Matthewjg95/PlatypusOne/services/ai/README.md

# services/ai

Skeleton — see docs/ROADMAP.md for the milestone that implements this service. Must follow the layering rule: depends only on platform interfaces and other services.
