Matthewjg95/PlatypusOne/docs/media/IMG_8050.JPG

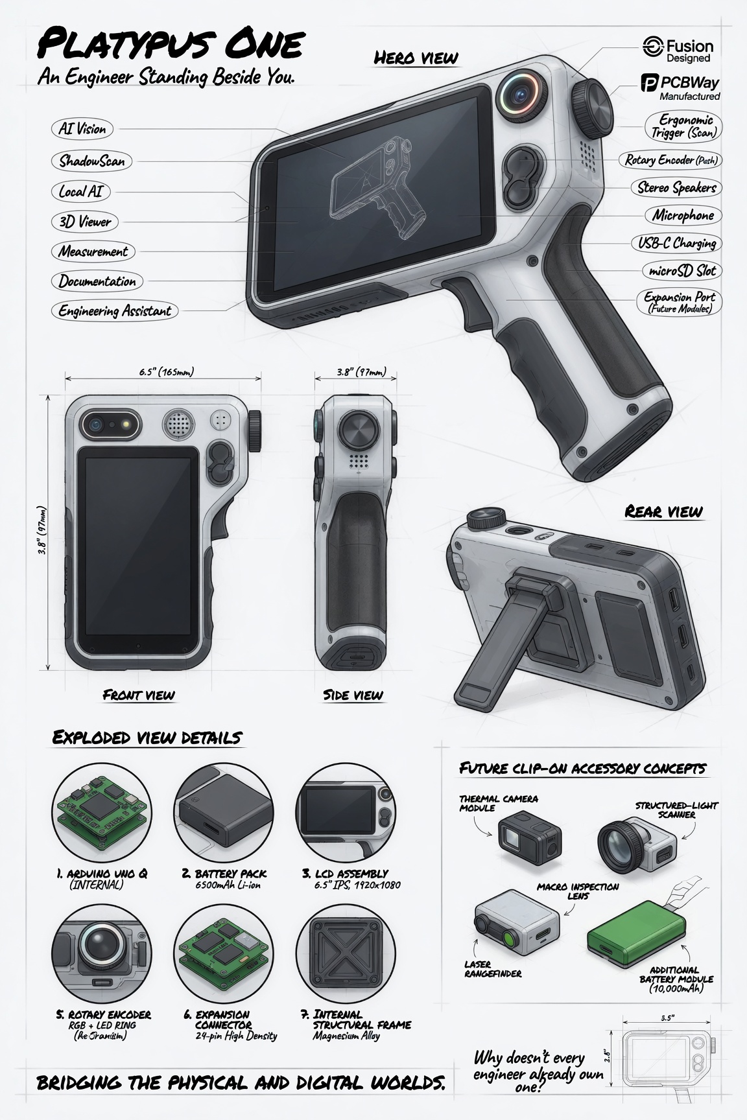
docs/media/IMG_8050.JPG
