Matthewjg95/PlatypusOne/docs/media/IMG_8051.JPG

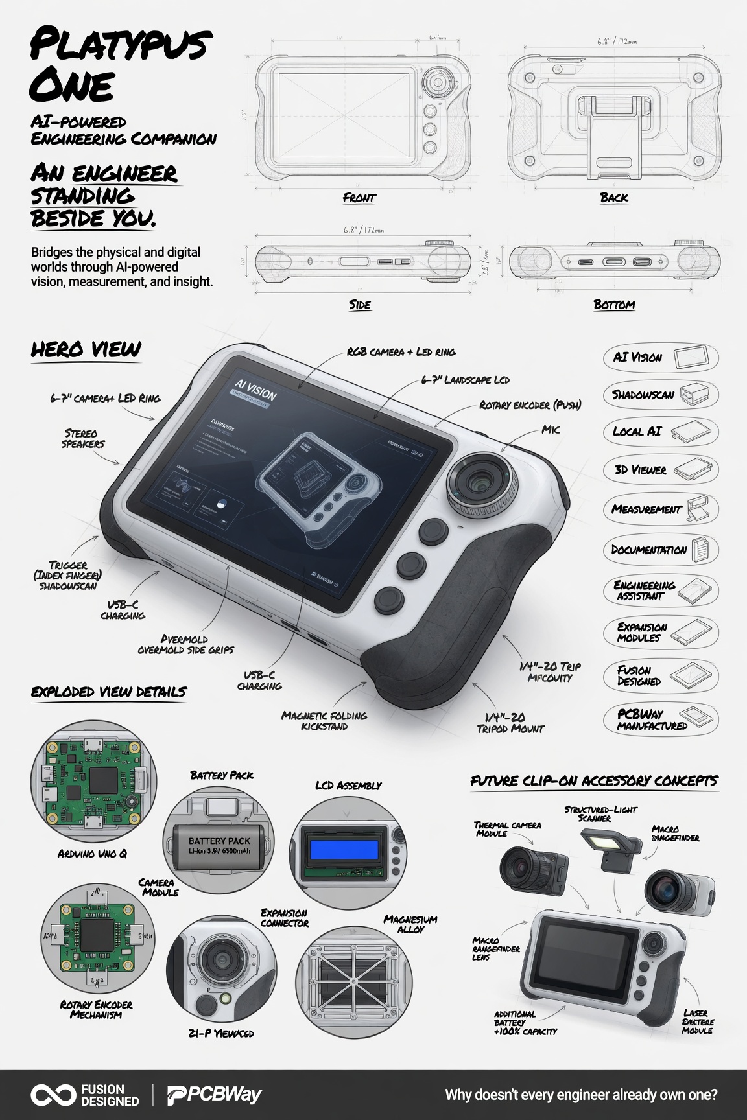
docs/media/IMG_8051.JPG
