Matthewjg95/PlatypusOne/docs/media/IMG_8052.JPG

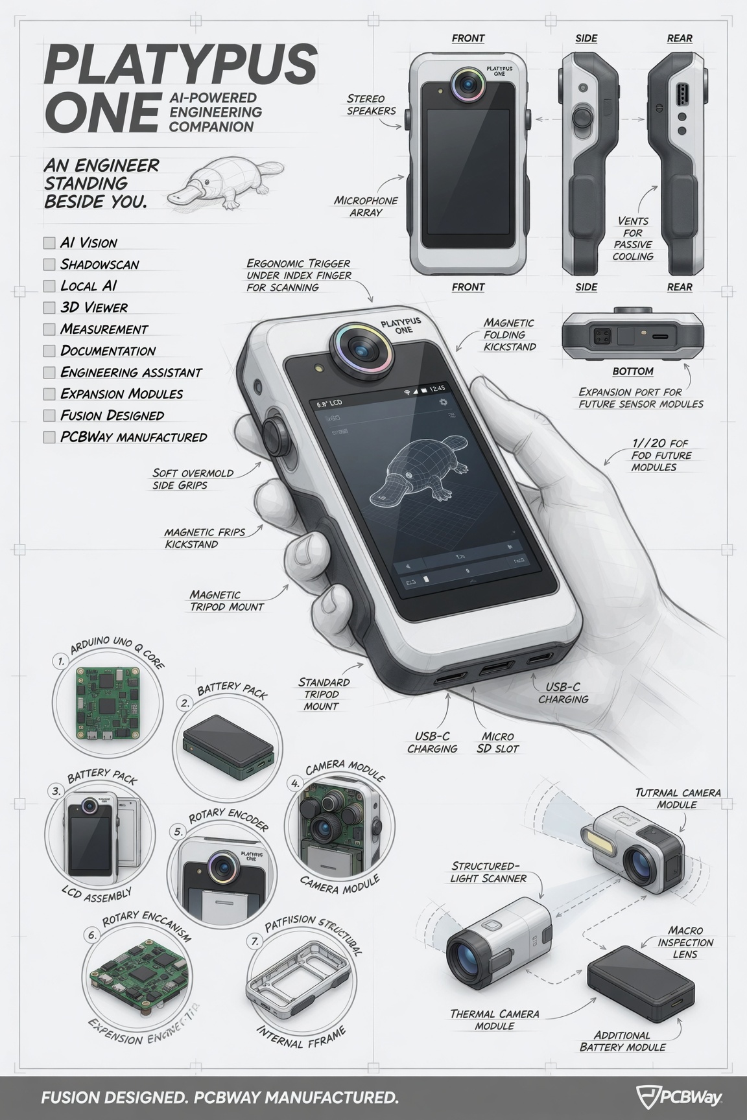
docs/media/IMG_8052.JPG
