Matthewjg95/PlatypusOne/docs/media/renders/scout-card-bolt.png

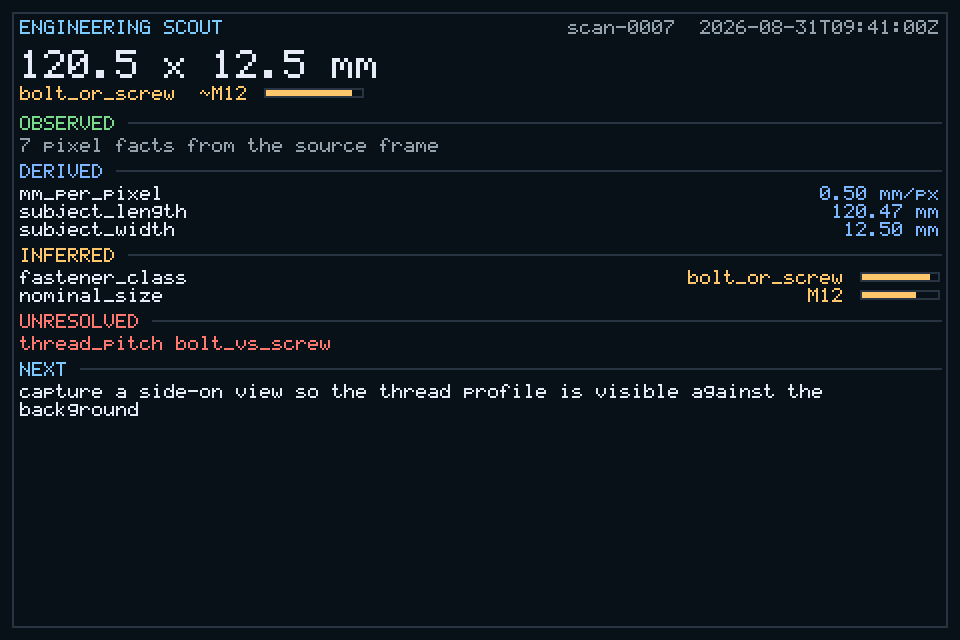
docs/media/renders/scout-card-bolt.png
