Matthewjg95/PlatypusOne/docs/hardware/calibration_sheet.pdf

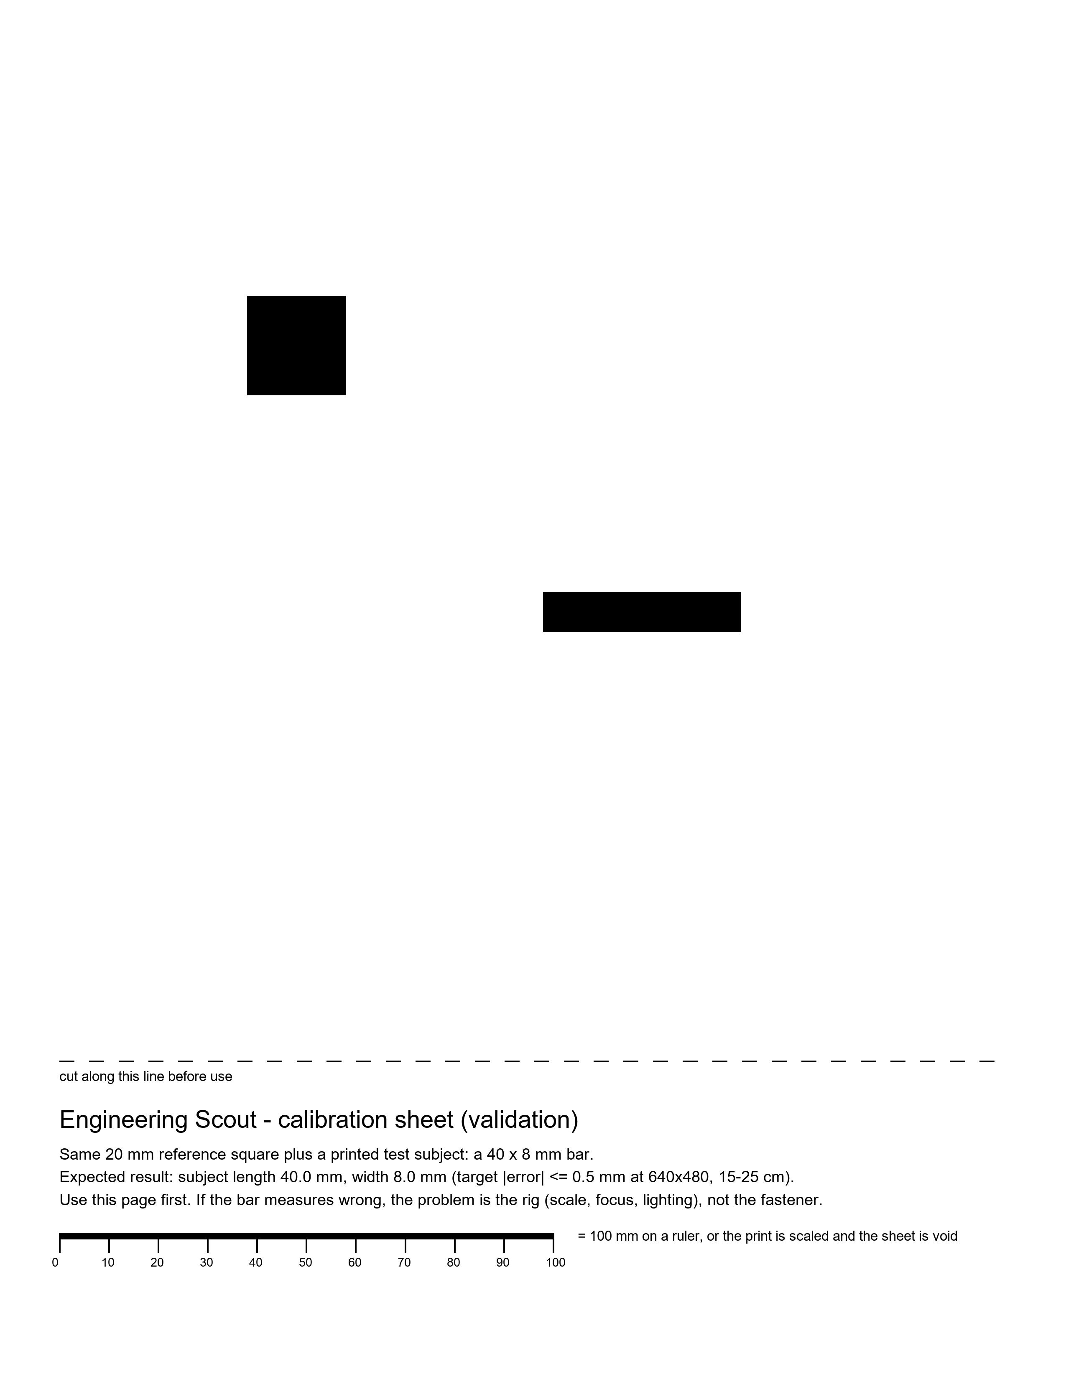
[picture p13: page 1]
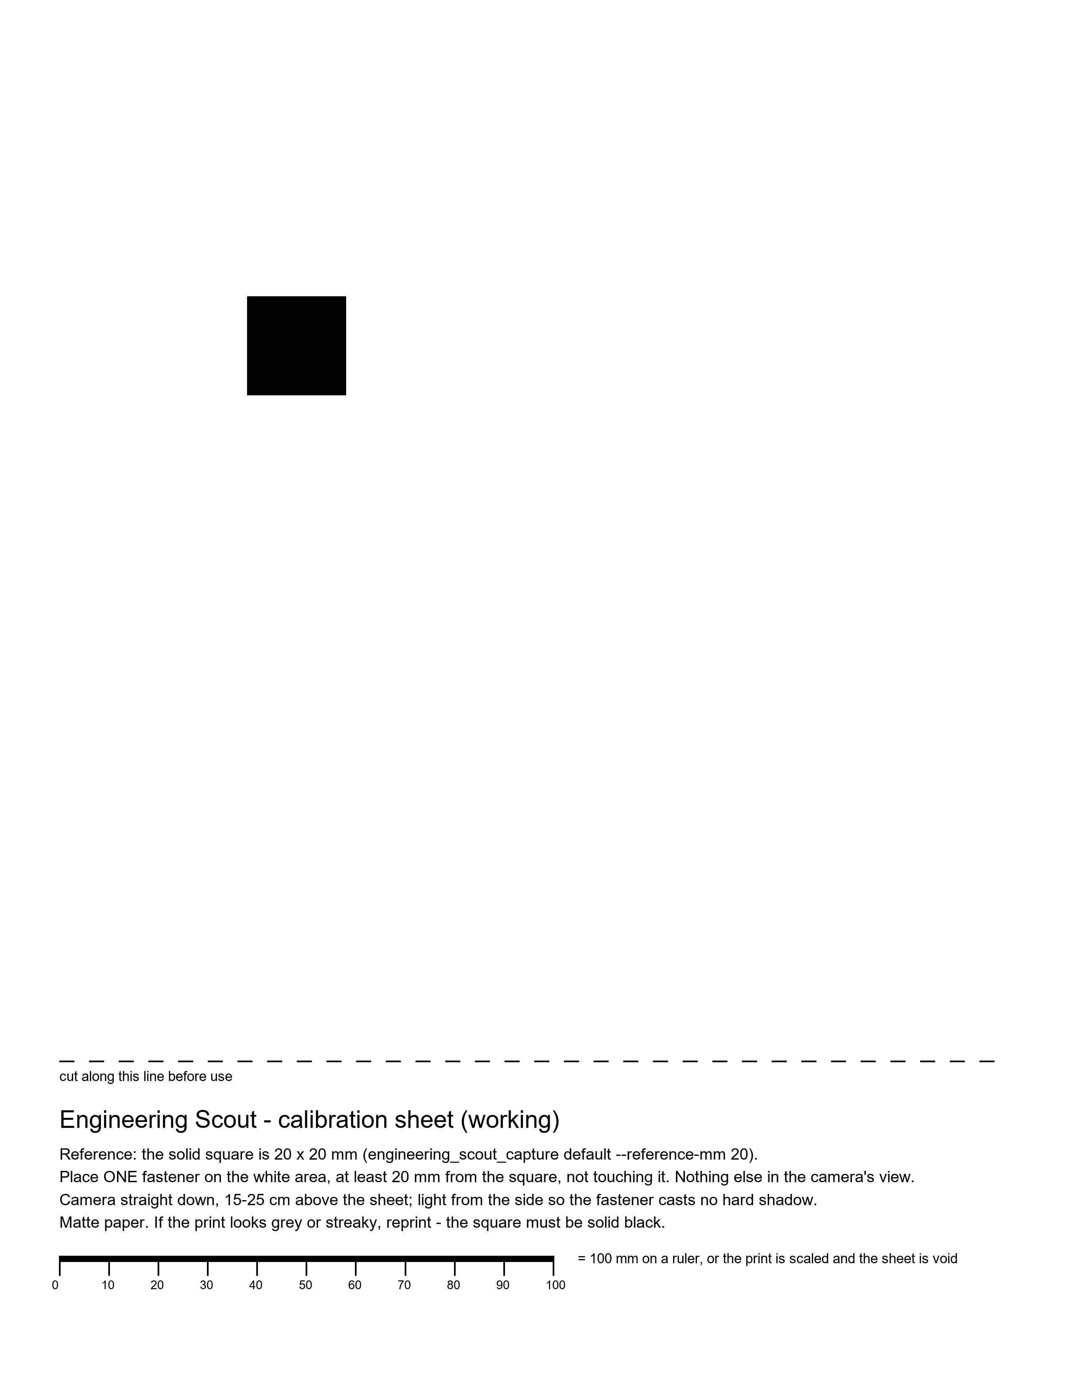
[picture p14: page 2]
