Matthewjg95/PlatypusOne/hardware/pcb/perception_head_rev_a/debug_test.kicad_sch

## KiCad design hardware/pcb/perception_head_rev_a/debug_test.kicad_sch (2026-10-05)

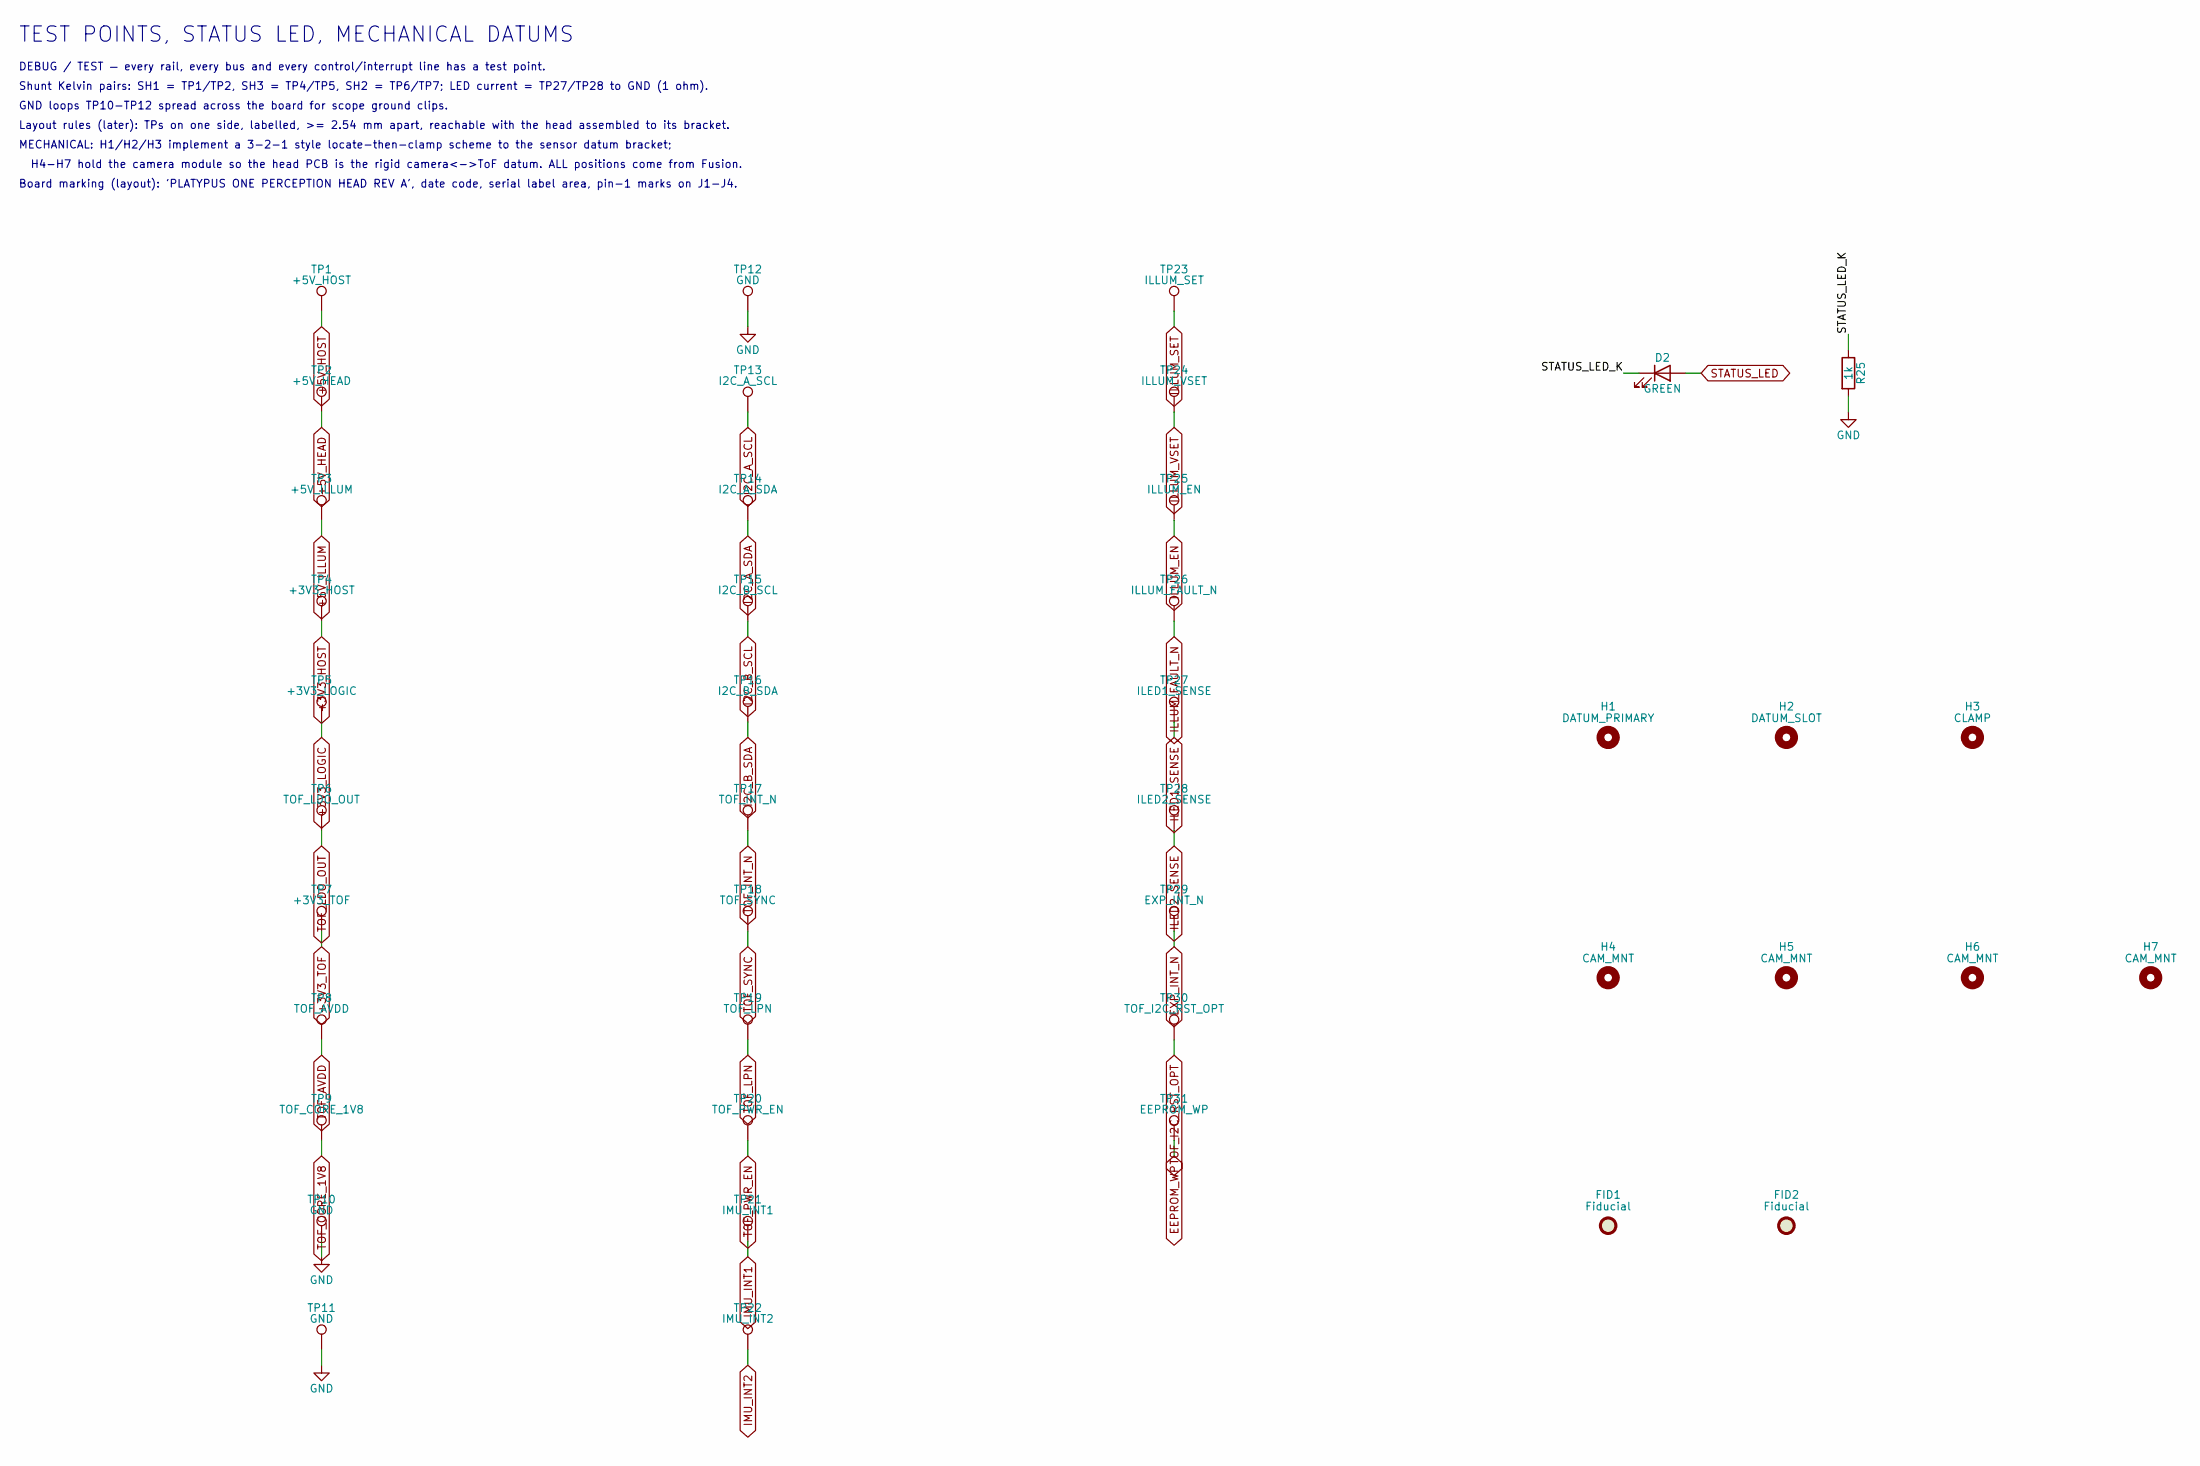
[picture p23: schematic debug_test.kicad_sch]

Parts:
D2: GREEN; LED_0603_1608Metric
FID1, FID2: Fiducial; Fiducial_1mm_Mask2mm
H1: DATUM_PRIMARY; MountingHole_2.2mm_M2
H2: DATUM_SLOT; MountingHole_2.2mm_M2
H3: CLAMP; MountingHole_2.2mm_M2
H4, H5, H6, H7: CAM_MNT; MountingHole_2.2mm_M2
R25: 1k; R_0603_1608Metric
TP1: +5V_HOST; TestPoint_Pad_D1.5mm
TP2: +5V_HEAD; TestPoint_Pad_D1.5mm
TP3: +5V_ILLUM; TestPoint_Pad_D1.5mm
TP4: +3V3_HOST; TestPoint_Pad_D1.5mm
TP5: +3V3_LOGIC; TestPoint_Pad_D1.5mm
TP6: TOF_LDO_OUT; TestPoint_Pad_D1.5mm
TP7: +3V3_TOF; TestPoint_Pad_D1.5mm
TP8: TOF_AVDD; TestPoint_Pad_D1.5mm
TP9: TOF_CORE_1V8; TestPoint_Pad_D1.5mm
TP10, TP11, TP12: GND; TestPoint_Keystone_5019_Miniature
TP13: I2C_A_SCL; TestPoint_Pad_D1.5mm
TP14: I2C_A_SDA; TestPoint_Pad_D1.5mm
TP15: I2C_B_SCL; TestPoint_Pad_D1.5mm
TP16: I2C_B_SDA; TestPoint_Pad_D1.5mm
TP17: TOF_INT_N; TestPoint_Pad_D1.5mm
TP18: TOF_SYNC; TestPoint_Pad_D1.5mm
TP19: TOF_LPN; TestPoint_Pad_D1.5mm
TP20: TOF_PWR_EN; TestPoint_Pad_D1.5mm
TP21: IMU_INT1; TestPoint_Pad_D1.5mm
TP22: IMU_INT2; TestPoint_Pad_D1.5mm
TP23: ILLUM_SET; TestPoint_Pad_D1.5mm
TP24: ILLUM_VSET; TestPoint_Pad_D1.5mm
TP25: ILLUM_EN; TestPoint_Pad_D1.5mm
TP26: ILLUM_FAULT_N; TestPoint_Pad_D1.5mm
TP27: ILED1_SENSE; TestPoint_Pad_D1.5mm
TP28: ILED2_SENSE; TestPoint_Pad_D1.5mm
TP29: EXP_INT_N; TestPoint_Pad_D1.5mm
TP30: TOF_I2C_RST_OPT; TestPoint_Pad_D1.5mm
TP31: EEPROM_WP; TestPoint_Pad_D1.5mm

Connections:
+3V3_HOST: TP4.1
+3V3_LOGIC: TP5.1
+3V3_TOF: TP7.1
+5V_HEAD: TP2.1
+5V_HOST: TP1.1
+5V_ILLUM: TP3.1
EEPROM_WP: TP31.1
EXP_INT_N: TP29.1
GND: R25.2, TP10.1, TP11.1, TP12.1
I2C_A_SCL: TP13.1
I2C_A_SDA: TP14.1
I2C_B_SCL: TP15.1
I2C_B_SDA: TP16.1
ILED1_SENSE: TP27.1
ILED2_SENSE: TP28.1
ILLUM_EN: TP25.1
ILLUM_FAULT_N: TP26.1
ILLUM_SET: TP23.1
ILLUM_VSET: TP24.1
IMU_INT1: TP21.1
IMU_INT2: TP22.1
STATUS_LED: D2.2 (A)
STATUS_LED_K: D2.1 (K), R25.1
TOF_AVDD: TP8.1
TOF_CORE_1V8: TP9.1
TOF_I2C_RST_OPT: TP30.1
TOF_INT_N: TP17.1
TOF_LDO_OUT: TP6.1
TOF_LPN: TP19.1
TOF_PWR_EN: TP20.1
TOF_SYNC: TP18.1

Notes on the sheet:
TEST POINTS, STATUS LED, MECHANICAL DATUMS
DEBUG / TEST — every rail, every bus and every control/interrupt line has a test point.
Shunt Kelvin pairs: SH1 = TP1/TP2, SH3 = TP4/TP5, SH2 = TP6/TP7; LED current = TP27/TP28 to GND (1 ohm).
GND loops TP10-TP12 spread across the board for scope ground clips.
Layout rules (later): TPs on one side, labelled, >= 2.54 mm apart, reachable with the head assembled to its bracket.
MECHANICAL: H1/H2/H3 implement a 3-2-1 style locate-then-clamp scheme to the sensor datum bracket;
H4-H7 hold the camera module so the head PCB is the rigid camera<->ToF datum. ALL positions come from Fusion.
Board marking (layout): 'PLATYPUS ONE PERCEPTION HEAD REV A', date code, serial label area, pin-1 marks on J1-J4.
