Matthewjg95/PlatypusOne/hardware/pcb/perception_head_rev_a/host_interface.kicad_sch

## KiCad design hardware/pcb/perception_head_rev_a/host_interface.kicad_sch (2026-10-05)

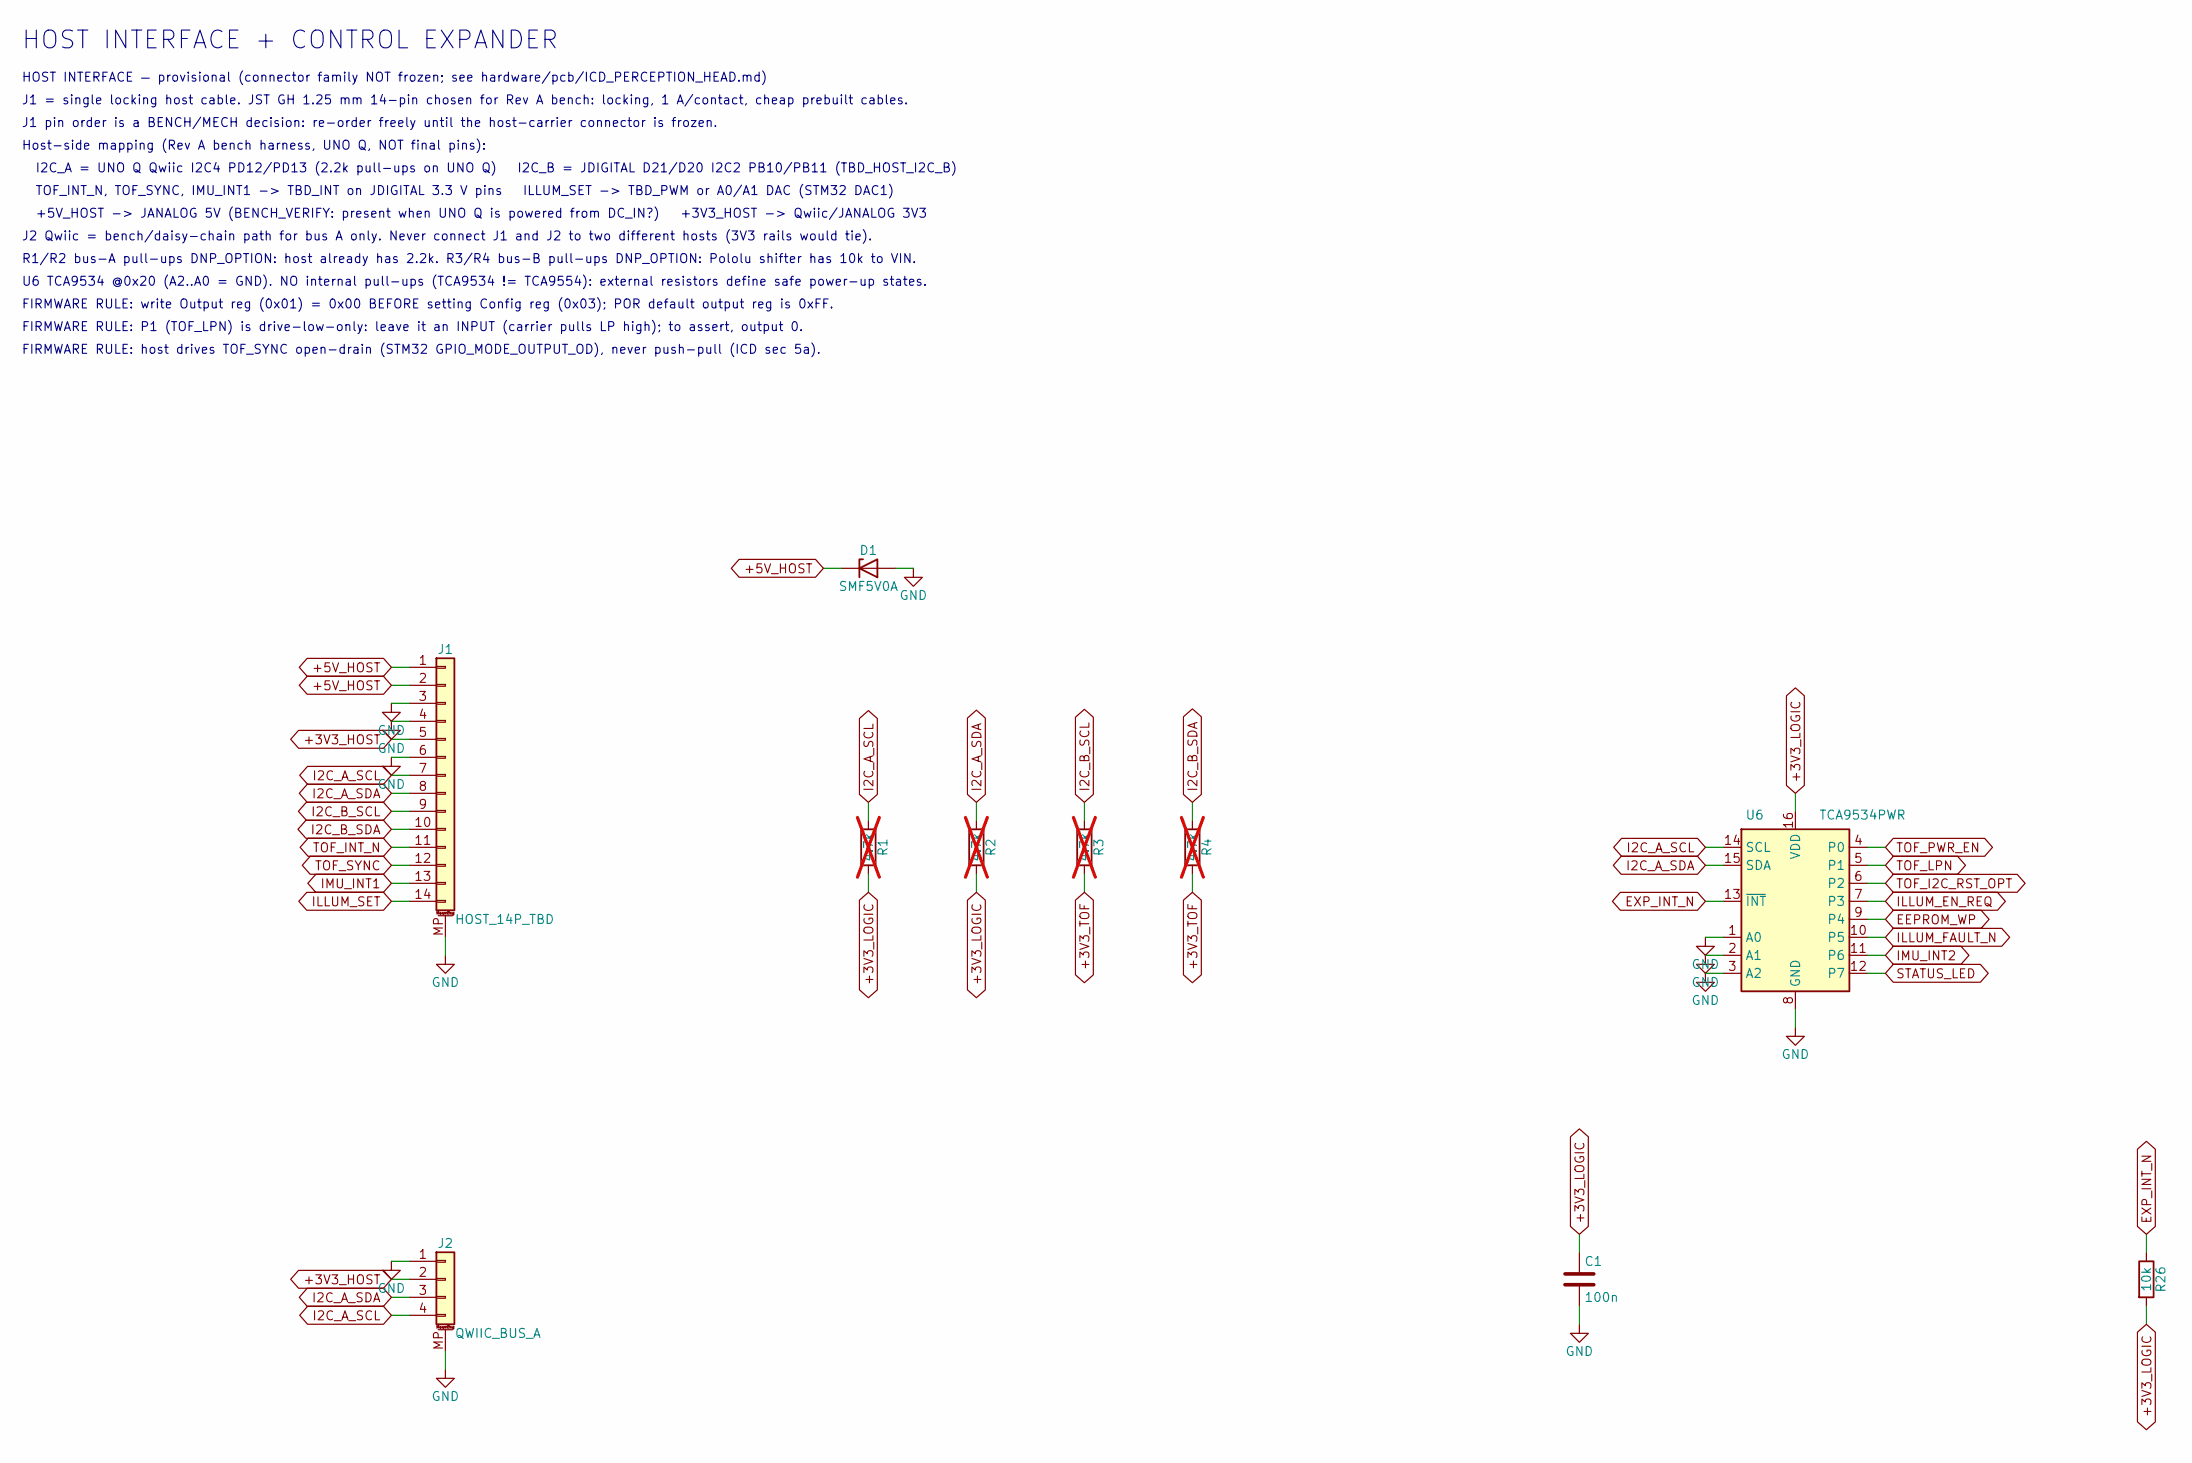
[picture p24: schematic host_interface.kicad_sch]

Parts:
C1: 100n; C_0603_1608Metric
D1: SMF5V0A; D_SMF; MPN SMF5V0A-E3-08
J1: HOST_14P_TBD; JST_GH_SM14B-GHS-TB_1x14-1MP_P1.25mm_Horizontal; MPN SM14B-GHS-TB(LF)(SN)
J2: QWIIC_BUS_A; JST_SH_SM04B-SRSS-TB_1x04-1MP_P1.00mm_Horizontal; MPN SM04B-SRSS-TB(LF)(SN)
R1, R2, R3, R4: 4.7k; R_0603_1608Metric; not fitted
R26: 10k; R_0603_1608Metric
U6: TCA9534PWR; TSSOP-16_4.4x5mm_P0.65mm; MPN TCA9534PWR

Connections:
+3V3_HOST: J1.5, J2.2
+3V3_LOGIC: C1.1, R1.2, R2.2, R26.2, U6.16 (VDD)
+3V3_TOF: R3.2, R4.2
+5V_HOST: D1.1 (K), J1.1, J1.2
EEPROM_WP: U6.9 (P4)
EXP_INT_N: R26.1, U6.13 (~INT)
GND: C1.2, D1.2 (A), J1.3, J1.4, J1.6, J1.MP (MountPin), J2.1, J2.MP (MountPin), U6.1 (A0), U6.2 (A1), U6.3 (A2), U6.8 (GND)
I2C_A_SCL: J1.7, J2.4, R1.1, U6.14 (SCL)
I2C_A_SDA: J1.8, J2.3, R2.1, U6.15 (SDA)
I2C_B_SCL: J1.9, R3.1
I2C_B_SDA: J1.10, R4.1
ILLUM_EN_REQ: U6.7 (P3)
ILLUM_FAULT_N: U6.10 (P5)
ILLUM_SET: J1.14
IMU_INT1: J1.13
IMU_INT2: U6.11 (P6)
STATUS_LED: U6.12 (P7)
TOF_I2C_RST_OPT: U6.6 (P2)
TOF_INT_N: J1.11
TOF_LPN: U6.5 (P1)
TOF_PWR_EN: U6.4 (P0)
TOF_SYNC: J1.12

Notes on the sheet:
HOST INTERFACE + CONTROL EXPANDER
HOST INTERFACE — provisional (connector family NOT frozen; see hardware/pcb/ICD_PERCEPTION_HEAD.md)
J1 = single locking host cable. JST GH 1.25 mm 14-pin chosen for Rev A bench: locking, 1 A/contact, cheap prebuilt cables.
J1 pin order is a BENCH/MECH decision: re-order freely until the host-carrier connector is frozen.
Host-side mapping (Rev A bench harness, UNO Q, NOT final pins):
I2C_A = UNO Q Qwiic I2C4 PD12/PD13 (2.2k pull-ups on UNO Q) I2C_B = JDIGITAL D21/D20 I2C2 PB10/PB11 (TBD_HOST_I2C_B)
TOF_INT_N, TOF_SYNC, IMU_INT1 -> TBD_INT on JDIGITAL 3.3 V pins ILLUM_SET -> TBD_PWM or A0/A1 DAC (STM32 DAC1)
+5V_HOST -> JANALOG 5V (BENCH_VERIFY: present when UNO Q is powered from DC_IN?) +3V3_HOST -> Qwiic/JANALOG 3V3
J2 Qwiic = bench/daisy-chain path for bus A only. Never connect J1 and J2 to two different hosts (3V3 rails would tie).
R1/R2 bus-A pull-ups DNP_OPTION: host already has 2.2k. R3/R4 bus-B pull-ups DNP_OPTION: Pololu shifter has 10k to VIN.
U6 TCA9534 @0x20 (A2..A0 = GND). NO internal pull-ups (TCA9534 != TCA9554): external resistors define safe power-up states.
FIRMWARE RULE: write Output reg (0x01) = 0x00 BEFORE setting Config reg (0x03); POR default output reg is 0xFF.
FIRMWARE RULE: P1 (TOF_LPN) is drive-low-only: leave it an INPUT (carrier pulls LP high); to assert, output 0.
FIRMWARE RULE: host drives TOF_SYNC open-drain (STM32 GPIO_MODE_OUTPUT_OD), never push-pull (ICD sec 5a).
