Matthewjg95/PlatypusOne/hardware/pcb/perception_head_rev_a/id_calibration.kicad_sch

## KiCad design hardware/pcb/perception_head_rev_a/id_calibration.kicad_sch (2026-10-05)

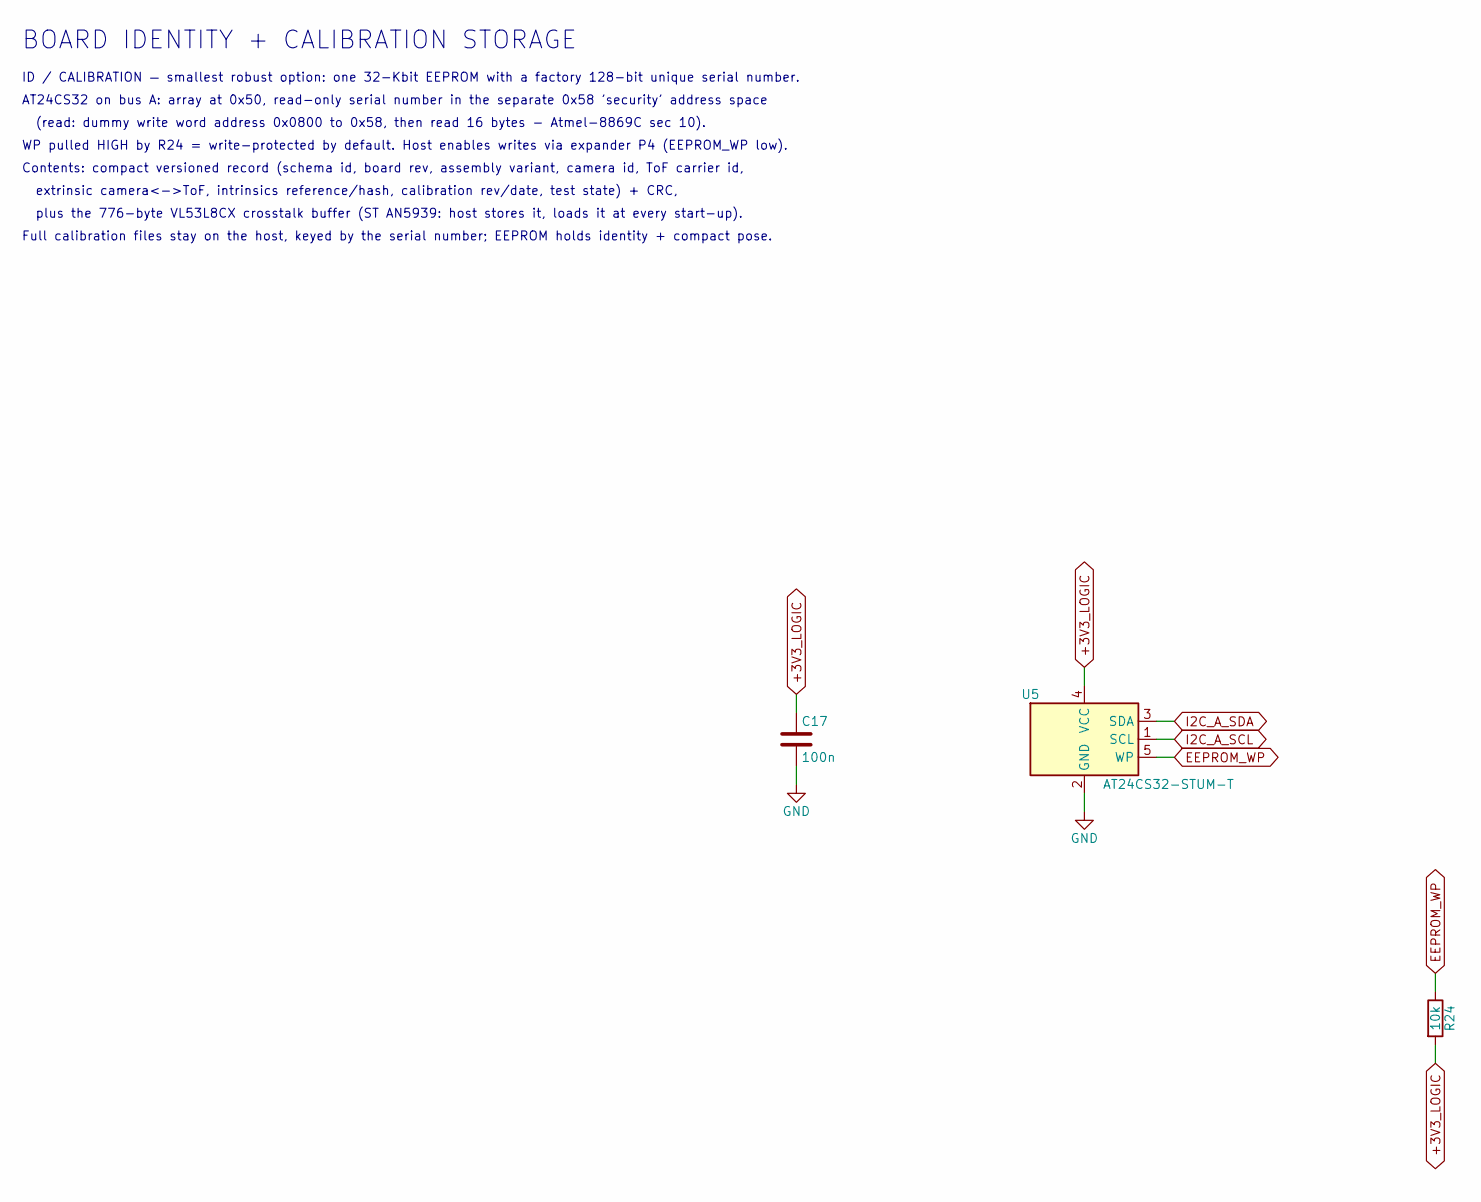
[picture p25: schematic id_calibration.kicad_sch]

Parts:
C17: 100n; C_0603_1608Metric
R24: 10k; R_0603_1608Metric
U5: AT24CS32-STUM-T; SOT-23-5; MPN AT24CS32-STUM-T

Connections:
+3V3_LOGIC: C17.1, R24.2, U5.4 (VCC)
EEPROM_WP: R24.1, U5.5 (WP)
GND: C17.2, U5.2 (GND)
I2C_A_SCL: U5.1 (SCL)
I2C_A_SDA: U5.3 (SDA)

Notes on the sheet:
BOARD IDENTITY + CALIBRATION STORAGE
ID / CALIBRATION — smallest robust option: one 32-Kbit EEPROM with a factory 128-bit unique serial number.
AT24CS32 on bus A: array at 0x50, read-only serial number in the separate 0x58 'security' address space
(read: dummy write word address 0x0800 to 0x58, then read 16 bytes - Atmel-8869C sec 10).
WP pulled HIGH by R24 = write-protected by default. Host enables writes via expander P4 (EEPROM_WP low).
Contents: compact versioned record (schema id, board rev, assembly variant, camera id, ToF carrier id,
extrinsic camera<->ToF, intrinsics reference/hash, calibration rev/date, test state) + CRC,
plus the 776-byte VL53L8CX crosstalk buffer (ST AN5939: host stores it, loads it at every start-up).
Full calibration files stay on the host, keyed by the serial number; EEPROM holds identity + compact pose.
