Matthewjg95/PlatypusOne/hardware/pcb/perception_head_rev_a/illumination.kicad_sch

## KiCad design hardware/pcb/perception_head_rev_a/illumination.kicad_sch (2026-10-05)

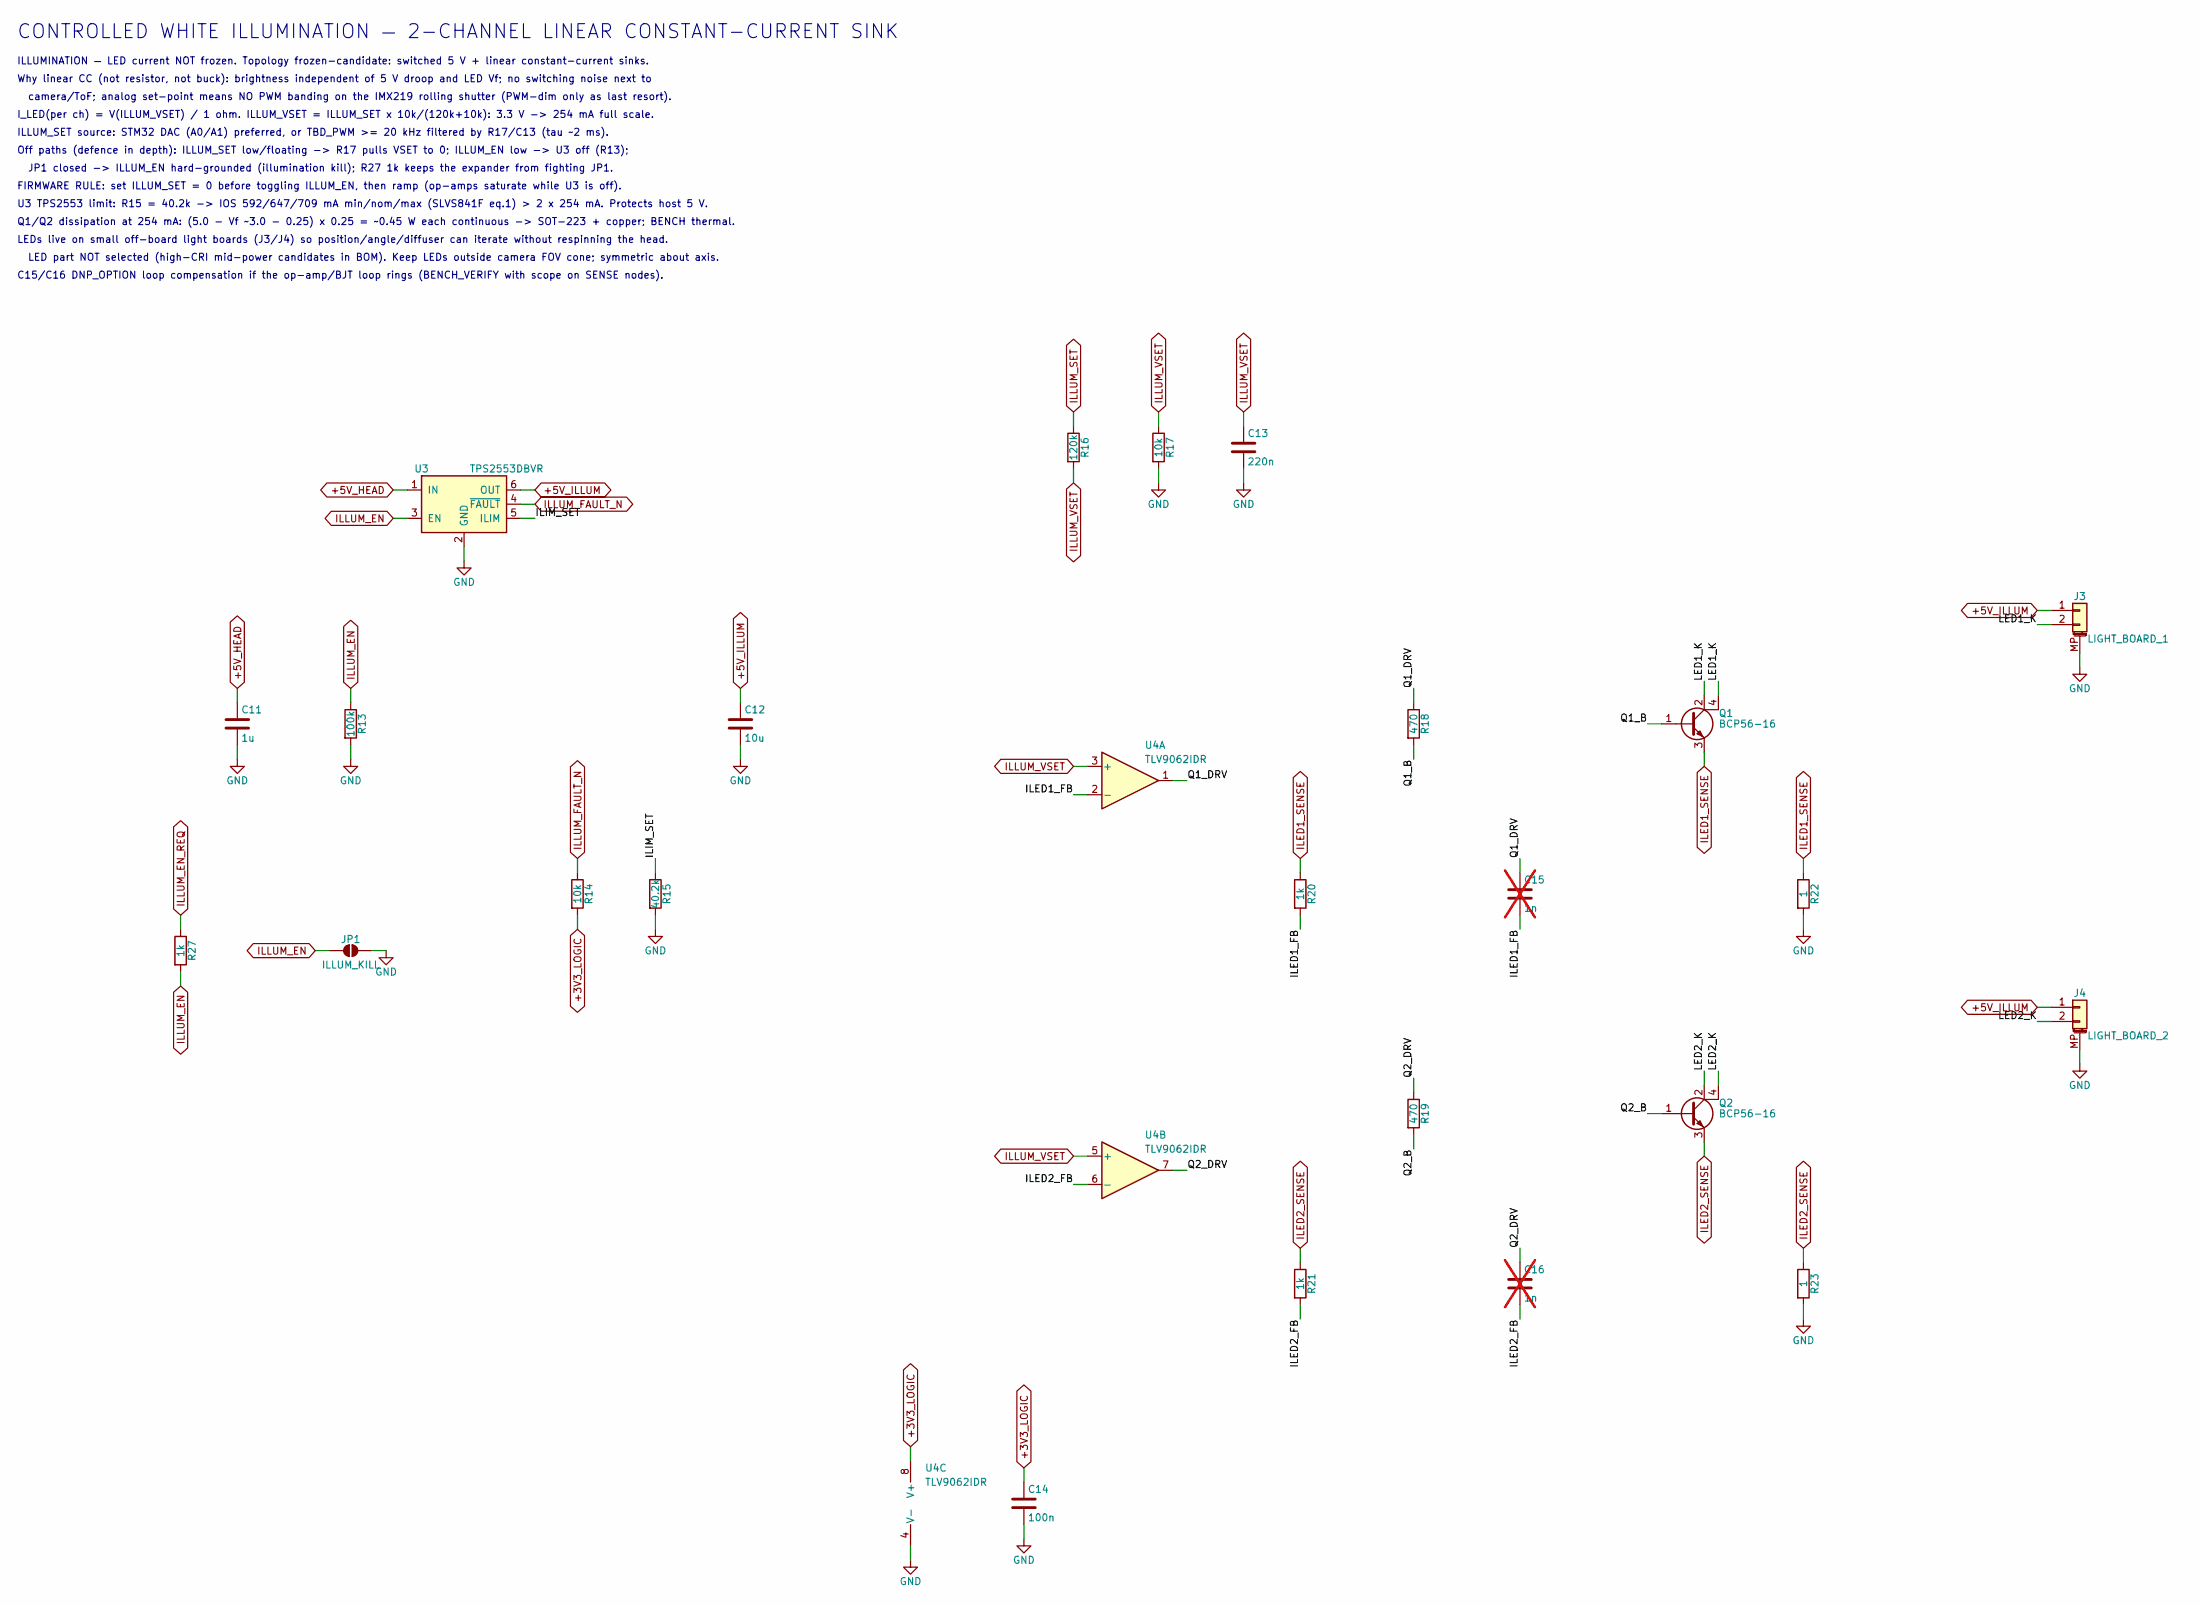
[picture p26: schematic illumination.kicad_sch]

Parts:
C11: 1u; C_0603_1608Metric
C12: 10u; C_0805_2012Metric
C13: 220n; C_0603_1608Metric
C14: 100n; C_0603_1608Metric
C15, C16: 1n; C_0603_1608Metric; not fitted
J3: LIGHT_BOARD_1; JST_GH_SM02B-GHS-TB_1x02-1MP_P1.25mm_Horizontal; MPN SM02B-GHS-TB(LF)(SN)
J4: LIGHT_BOARD_2; JST_GH_SM02B-GHS-TB_1x02-1MP_P1.25mm_Horizontal; MPN SM02B-GHS-TB(LF)(SN)
JP1: ILLUM_KILL; SolderJumper-2_P1.3mm_Open_RoundedPad1.0x1.5mm
Q1, Q2: BCP56-16; SOT-223-3_TabPin2; MPN BCP56-16,115
R13: 100k; R_0603_1608Metric
R14, R17: 10k; R_0603_1608Metric
R15: 40.2k; R_0603_1608Metric
R16: 120k; R_0603_1608Metric
R18, R19: 470; R_0603_1608Metric
R20, R21, R27: 1k; R_0603_1608Metric
R22, R23: 1; R_1206_3216Metric
U3: TPS2553DBVR; SOT-23-6; MPN TPS2553DBVR
U4: TLV9062IDR; SOIC-8_3.9x4.9mm_P1.27mm; MPN TLV9062IDR

Connections:
+3V3_LOGIC: C14.1, R14.2, U4.8 (V+)
+5V_HEAD: C11.1, U3.1 (IN)
+5V_ILLUM: C12.1, J3.1, J4.1, U3.6 (OUT)
GND: C11.2, C12.2, C13.2, C14.2, J3.MP (MountPin), J4.MP (MountPin), JP1.2 (B), R13.2, R15.2, R17.2, R22.2, R23.2, U3.2 (GND), U4.4 (V-)
ILED1_FB: C15.2, R20.2, U4.2 (-)
ILED1_SENSE: Q1.3 (E), R20.1, R22.1
ILED2_FB: C16.2, R21.2, U4.6 (-)
ILED2_SENSE: Q2.3 (E), R21.1, R23.1
ILIM_SET: R15.1, U3.5 (ILIM)
ILLUM_EN: JP1.1 (A), R13.1, R27.2, U3.3 (EN)
ILLUM_EN_REQ: R27.1
ILLUM_FAULT_N: R14.1, U3.4 (~FAULT)
ILLUM_SET: R16.1
ILLUM_VSET: C13.1, R16.2, R17.1, U4.3 (+), U4.5 (+)
LED1_K: J3.2, Q1.2 (C), Q1.4 (C)
LED2_K: J4.2, Q2.2 (C), Q2.4 (C)
Q1_B: Q1.1 (B), R18.2
Q1_DRV: C15.1, R18.1, U4.1
Q2_B: Q2.1 (B), R19.2
Q2_DRV: C16.1, R19.1, U4.7

Notes on the sheet:
CONTROLLED WHITE ILLUMINATION — 2-CHANNEL LINEAR CONSTANT-CURRENT SINK
ILLUMINATION — LED current NOT frozen. Topology frozen-candidate: switched 5 V + linear constant-current sinks.
Why linear CC (not resistor, not buck): brightness independent of 5 V droop and LED Vf; no switching noise next to
camera/ToF; analog set-point means NO PWM banding on the IMX219 rolling shutter (PWM-dim only as last resort).
I_LED(per ch) = V(ILLUM_VSET) / 1 ohm. ILLUM_VSET = ILLUM_SET x 10k/(120k+10k): 3.3 V -> 254 mA full scale.
ILLUM_SET source: STM32 DAC (A0/A1) preferred, or TBD_PWM >= 20 kHz filtered by R17/C13 (tau ~2 ms).
Off paths (defence in depth): ILLUM_SET low/floating -> R17 pulls VSET to 0; ILLUM_EN low -> U3 off (R13);
JP1 closed -> ILLUM_EN hard-grounded (illumination kill); R27 1k keeps the expander from fighting JP1.
FIRMWARE RULE: set ILLUM_SET = 0 before toggling ILLUM_EN, then ramp (op-amps saturate while U3 is off).
U3 TPS2553 limit: R15 = 40.2k -> IOS 592/647/709 mA min/nom/max (SLVS841F eq.1) > 2 x 254 mA. Protects host 5 V.
Q1/Q2 dissipation at 254 mA: (5.0 - Vf ~3.0 - 0.25) x 0.25 = ~0.45 W each continuous -> SOT-223 + copper; BENCH thermal.
LEDs live on small off-board light boards (J3/J4) so position/angle/diffuser can iterate without respinning the head.
LED part NOT selected (high-CRI mid-power candidates in BOM). Keep LEDs outside camera FOV cone; symmetric about axis.
C15/C16 DNP_OPTION loop compensation if the op-amp/BJT loop rings (BENCH_VERIFY with scope on SENSE nodes).
