Matthewjg95/PlatypusOne/hardware/pcb/perception_head_rev_a/imu.kicad_sch

## KiCad design hardware/pcb/perception_head_rev_a/imu.kicad_sch (2026-10-05)

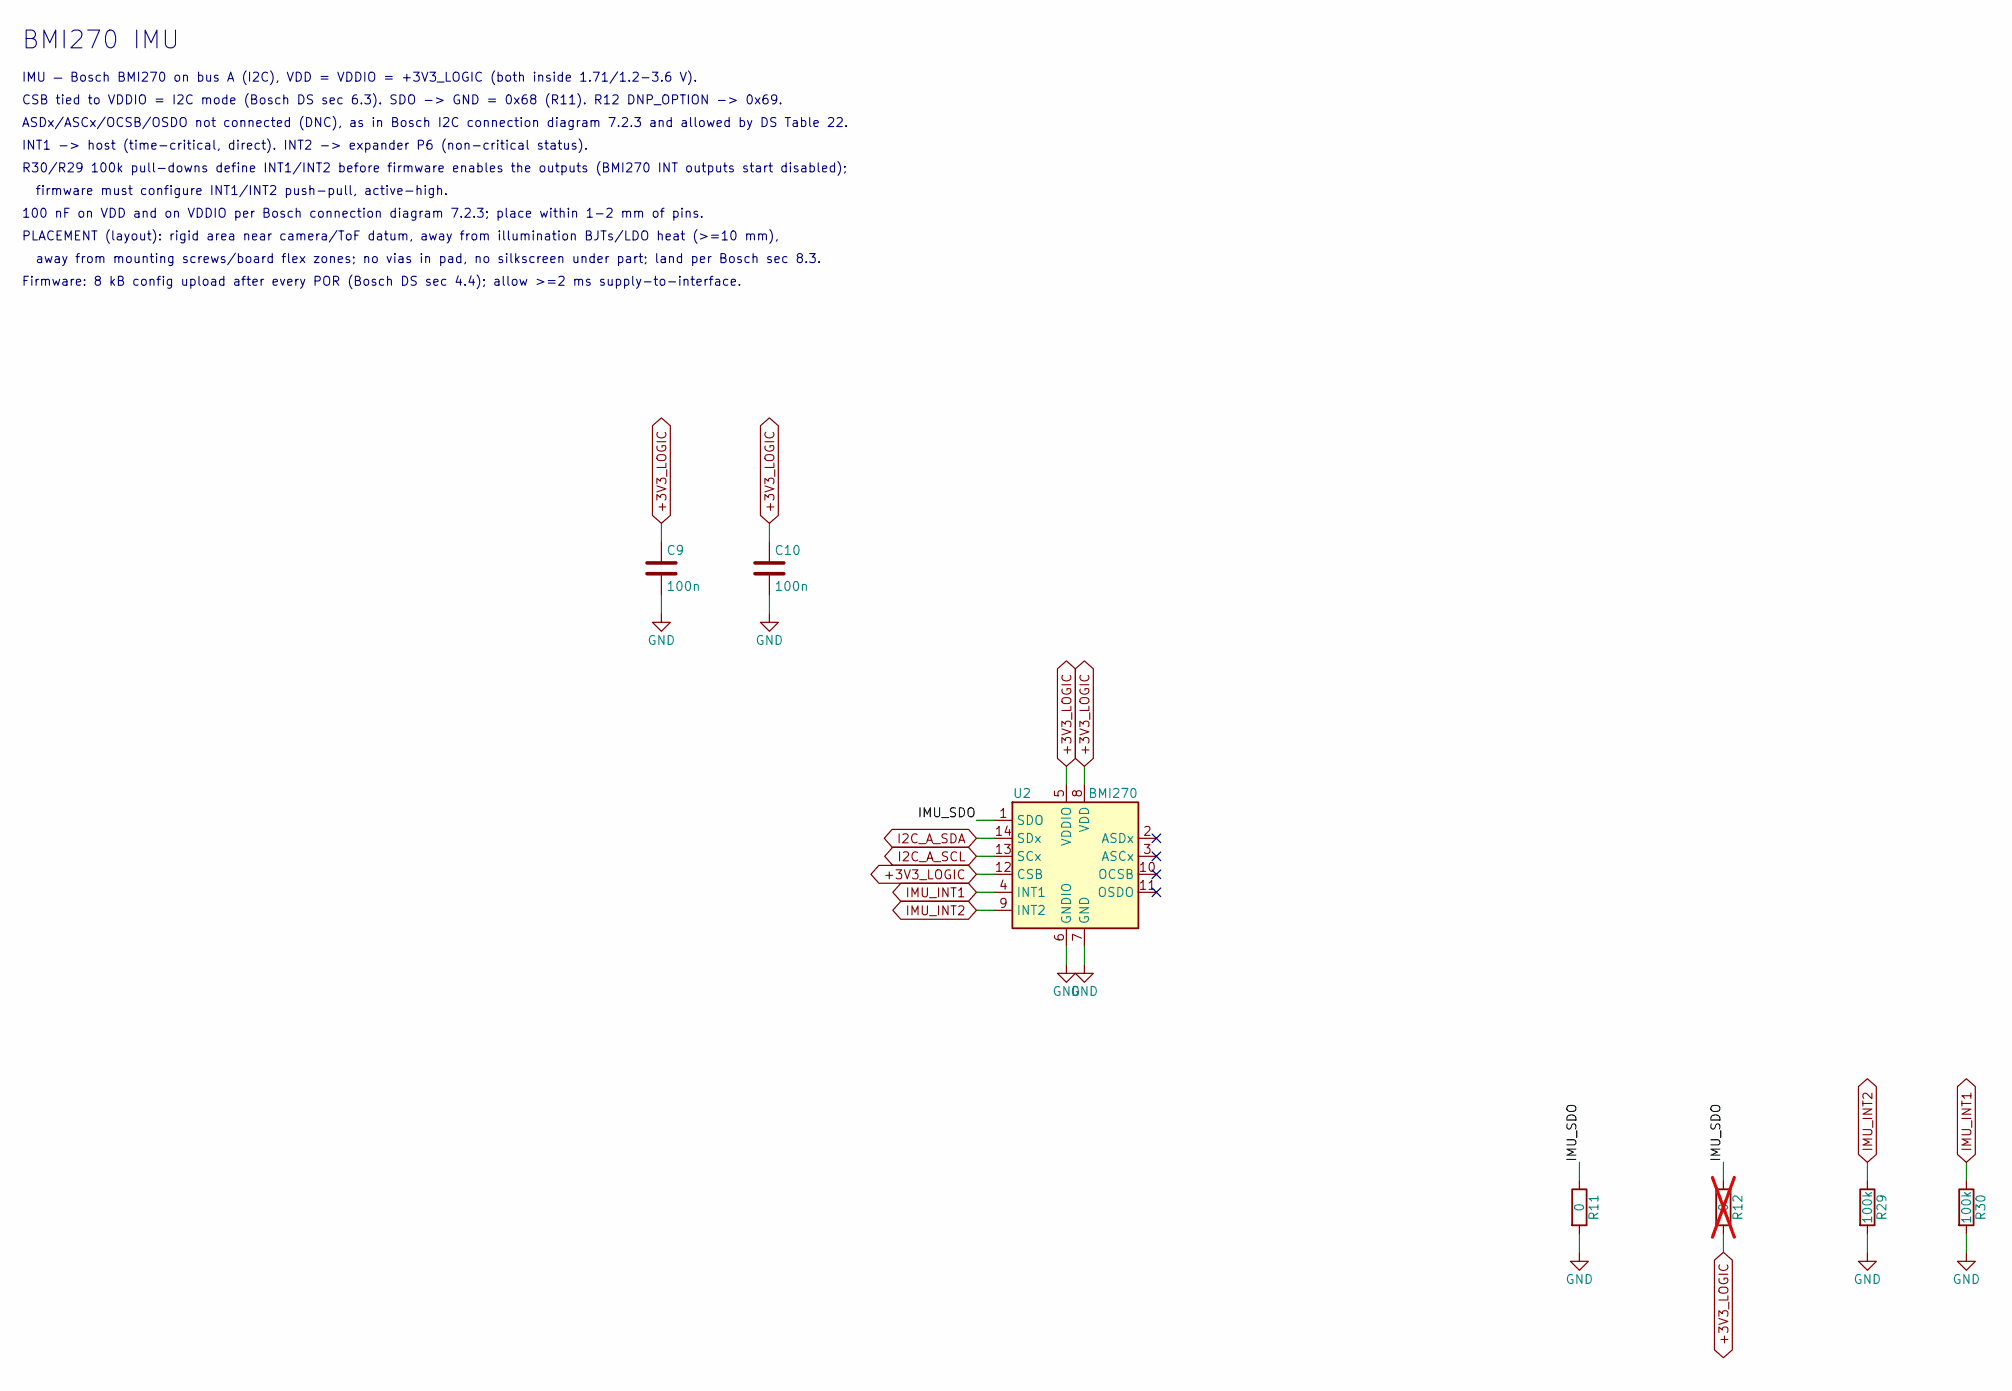
[picture p27: schematic imu.kicad_sch]

Parts:
C9, C10: 100n; C_0603_1608Metric
R11: 0; R_0603_1608Metric
R12: 0; R_0603_1608Metric; not fitted
R29, R30: 100k; R_0603_1608Metric
U2: BMI270; Bosch_LGA-14_3x2.5mm_P0.5mm_BoschLand; MPN BMI270

Connections:
+3V3_LOGIC: C9.1, C10.1, R12.2, U2.5 (VDDIO), U2.8 (VDD), U2.12 (CSB)
GND: C9.2, C10.2, R11.2, R29.2, R30.2, U2.6 (GNDIO), U2.7 (GND)
I2C_A_SCL: U2.13 (SCx)
I2C_A_SDA: U2.14 (SDx)
IMU_INT1: R30.1, U2.4 (INT1)
IMU_INT2: R29.1, U2.9 (INT2)
IMU_SDO: R11.1, R12.1, U2.1 (SDO)

Notes on the sheet:
BMI270 IMU
IMU — Bosch BMI270 on bus A (I2C), VDD = VDDIO = +3V3_LOGIC (both inside 1.71/1.2-3.6 V).
CSB tied to VDDIO = I2C mode (Bosch DS sec 6.3). SDO -> GND = 0x68 (R11). R12 DNP_OPTION -> 0x69.
ASDx/ASCx/OCSB/OSDO not connected (DNC), as in Bosch I2C connection diagram 7.2.3 and allowed by DS Table 22.
INT1 -> host (time-critical, direct). INT2 -> expander P6 (non-critical status).
R30/R29 100k pull-downs define INT1/INT2 before firmware enables the outputs (BMI270 INT outputs start disabled);
firmware must configure INT1/INT2 push-pull, active-high.
100 nF on VDD and on VDDIO per Bosch connection diagram 7.2.3; place within 1-2 mm of pins.
PLACEMENT (layout): rigid area near camera/ToF datum, away from illumination BJTs/LDO heat (>=10 mm),
away from mounting screws/board flex zones; no vias in pad, no silkscreen under part; land per Bosch sec 8.3.
Firmware: 8 kB config upload after every POR (Bosch DS sec 4.4); allow >=2 ms supply-to-interface.
