Matthewjg95/PlatypusOne/hardware/pcb/perception_head_rev_a/power.kicad_sch

## KiCad design hardware/pcb/perception_head_rev_a/power.kicad_sch (2026-10-05)

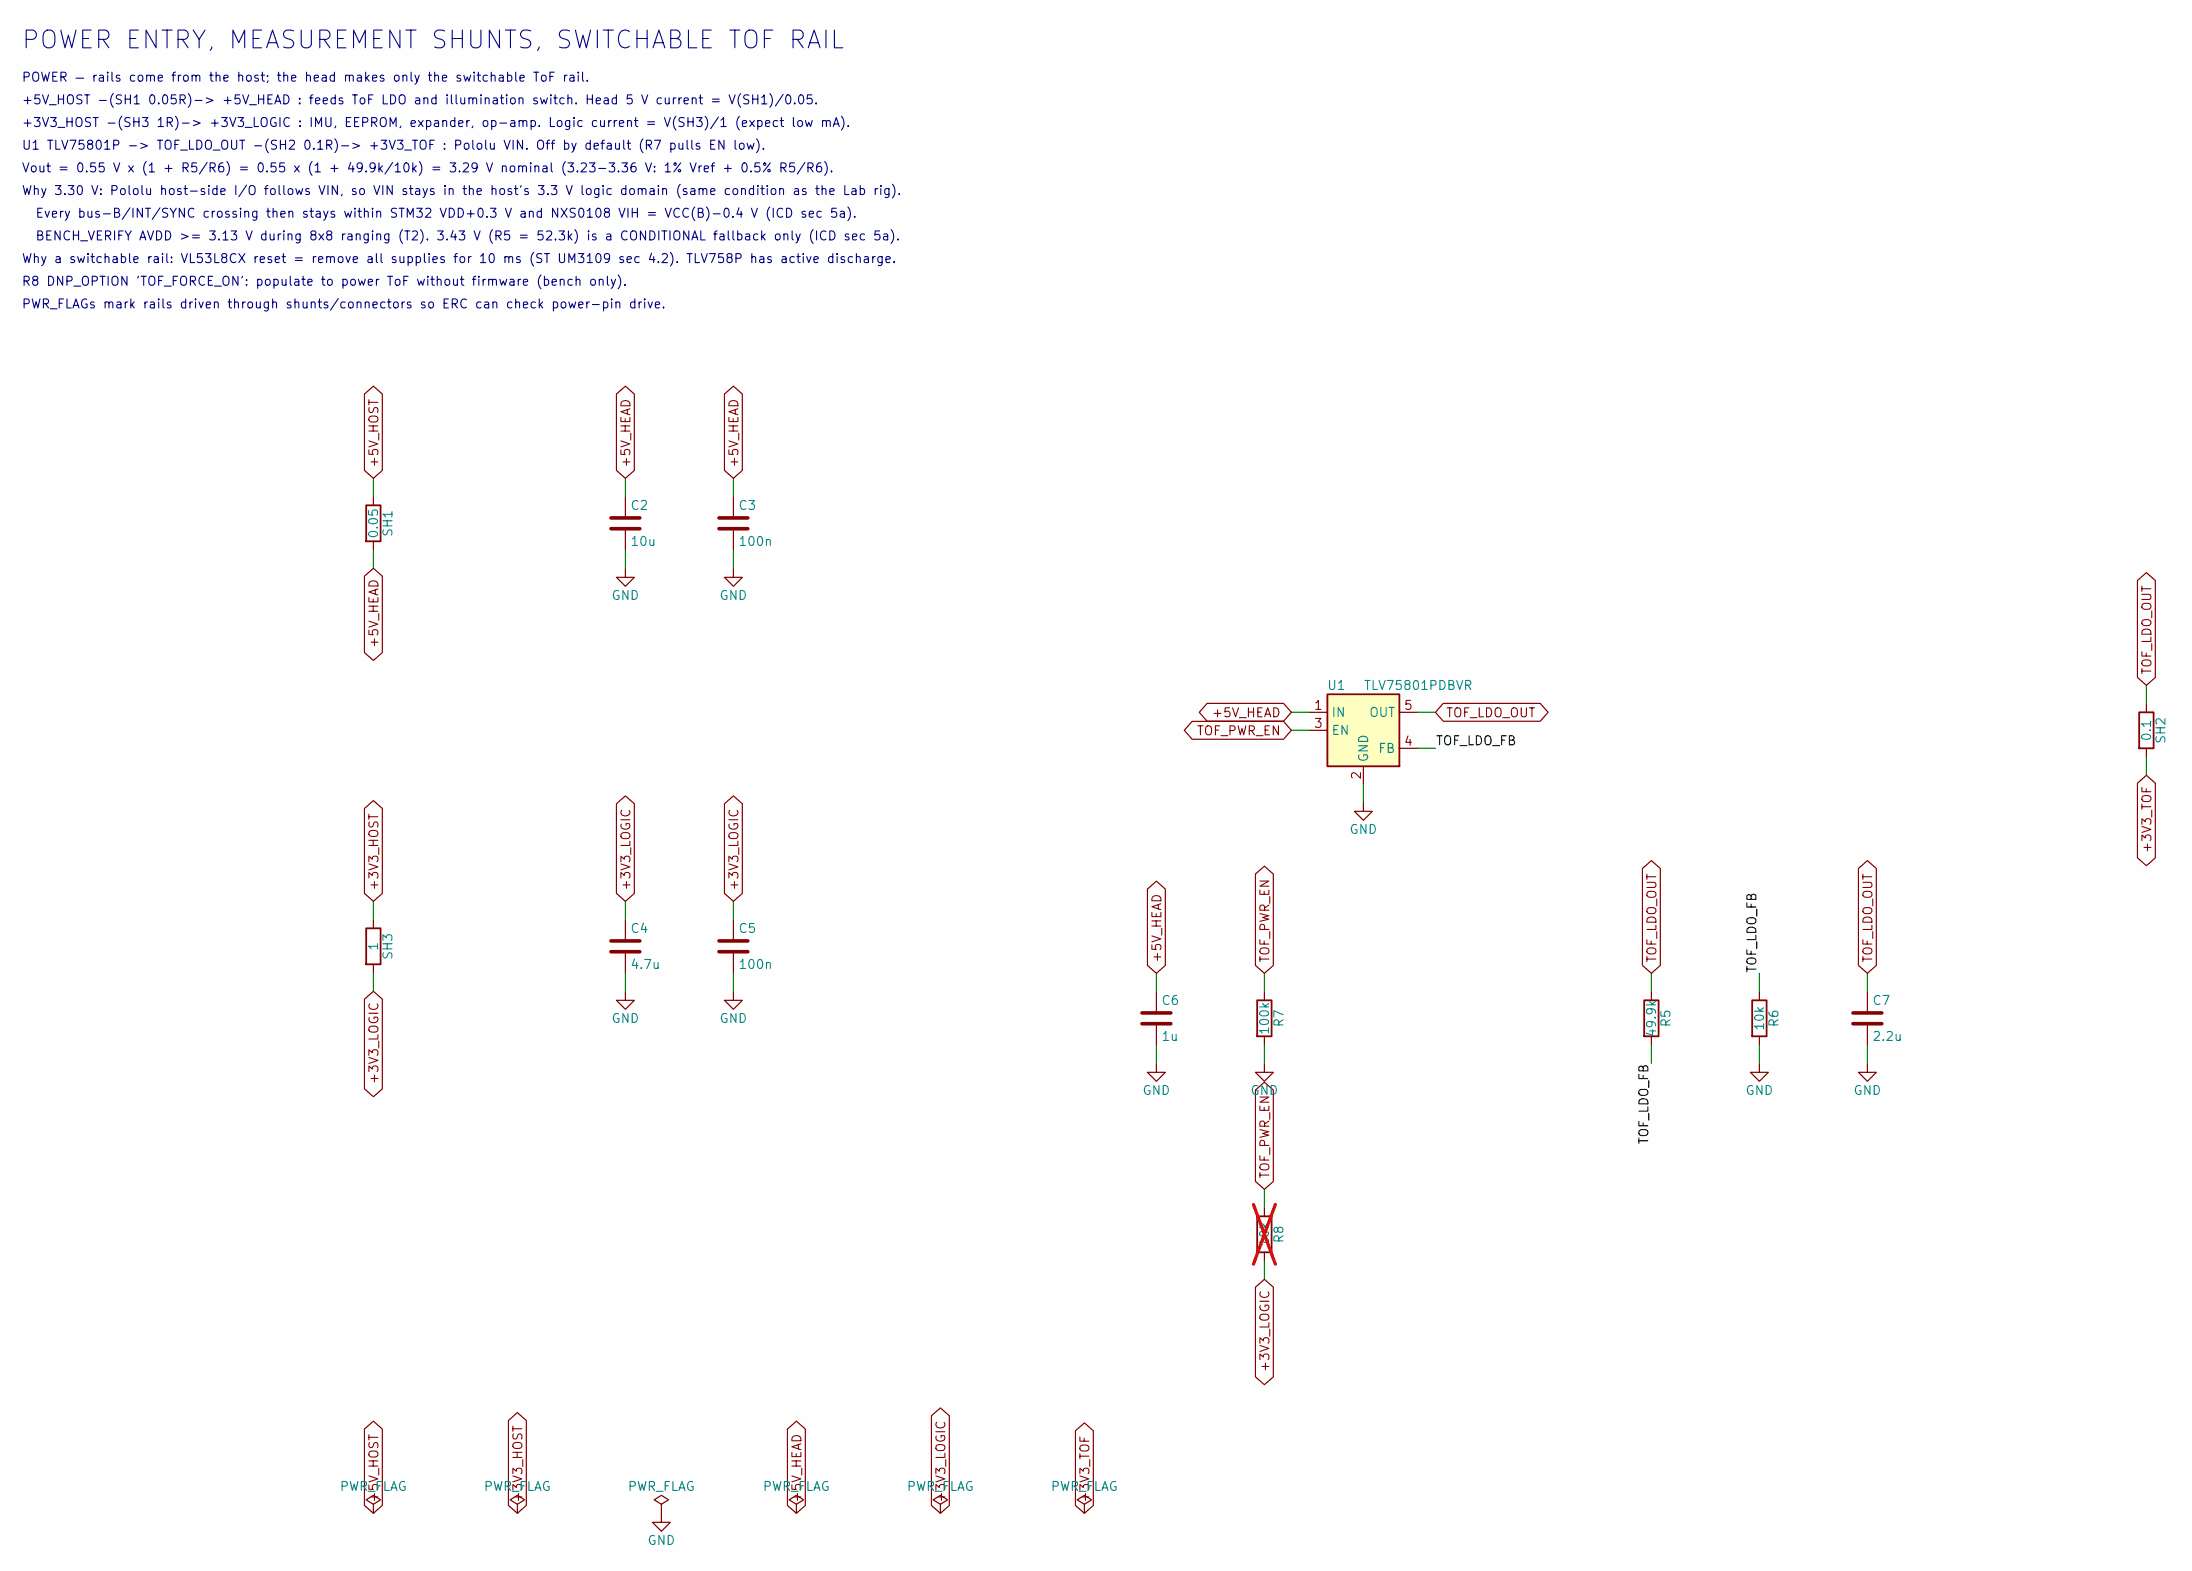
[picture p28: schematic power.kicad_sch]

Parts:
C2: 10u; C_0805_2012Metric
C3, C5: 100n; C_0603_1608Metric
C4: 4.7u; C_0805_2012Metric
C6: 1u; C_0603_1608Metric
C7: 2.2u; C_0805_2012Metric
R5: 49.9k; R_0603_1608Metric
R6: 10k; R_0603_1608Metric
R7: 100k; R_0603_1608Metric
R8: 10k; R_0603_1608Metric; not fitted
SH1: 0.05; R_1206_3216Metric
SH2: 0.1; R_0805_2012Metric
SH3: 1; R_0603_1608Metric
U1: TLV75801PDBVR; SOT-23-5; MPN TLV75801PDBVR

Connections:
+3V3_HOST: SH3.1
+3V3_LOGIC: C4.1, C5.1, R8.2, SH3.2
+3V3_TOF: SH2.2
+5V_HEAD: C2.1, C3.1, C6.1, SH1.2, U1.1 (IN)
+5V_HOST: SH1.1
GND: C2.2, C3.2, C4.2, C5.2, C6.2, C7.2, R6.2, R7.2, U1.2 (GND)
TOF_LDO_FB: R5.2, R6.1, U1.4 (FB)
TOF_LDO_OUT: C7.1, R5.1, SH2.1, U1.5 (OUT)
TOF_PWR_EN: R7.1, R8.1, U1.3 (EN)

Notes on the sheet:
POWER ENTRY, MEASUREMENT SHUNTS, SWITCHABLE TOF RAIL
POWER — rails come from the host; the head makes only the switchable ToF rail.
+5V_HOST -(SH1 0.05R)-> +5V_HEAD : feeds ToF LDO and illumination switch. Head 5 V current = V(SH1)/0.05.
+3V3_HOST -(SH3 1R)-> +3V3_LOGIC : IMU, EEPROM, expander, op-amp. Logic current = V(SH3)/1 (expect low mA).
U1 TLV75801P -> TOF_LDO_OUT -(SH2 0.1R)-> +3V3_TOF : Pololu VIN. Off by default (R7 pulls EN low).
Vout = 0.55 V x (1 + R5/R6) = 0.55 x (1 + 49.9k/10k) = 3.29 V nominal (3.23-3.36 V: 1% Vref + 0.5% R5/R6).
Why 3.30 V: Pololu host-side I/O follows VIN, so VIN stays in the host's 3.3 V logic domain (same condition as the Lab rig).
Every bus-B/INT/SYNC crossing then stays within STM32 VDD+0.3 V and NXS0108 VIH = VCC(B)-0.4 V (ICD sec 5a).
BENCH_VERIFY AVDD >= 3.13 V during 8x8 ranging (T2). 3.43 V (R5 = 52.3k) is a CONDITIONAL fallback only (ICD sec 5a).
Why a switchable rail: VL53L8CX reset = remove all supplies for 10 ms (ST UM3109 sec 4.2). TLV758P has active discharge.
R8 DNP_OPTION 'TOF_FORCE_ON': populate to power ToF without firmware (bench only).
PWR_FLAGs mark rails driven through shunts/connectors so ERC can check power-pin drive.
