Matthewjg95/PlatypusOne/hardware/pcb/perception_head_rev_a/tof.kicad_sch

## KiCad design hardware/pcb/perception_head_rev_a/tof.kicad_sch (2026-10-05)

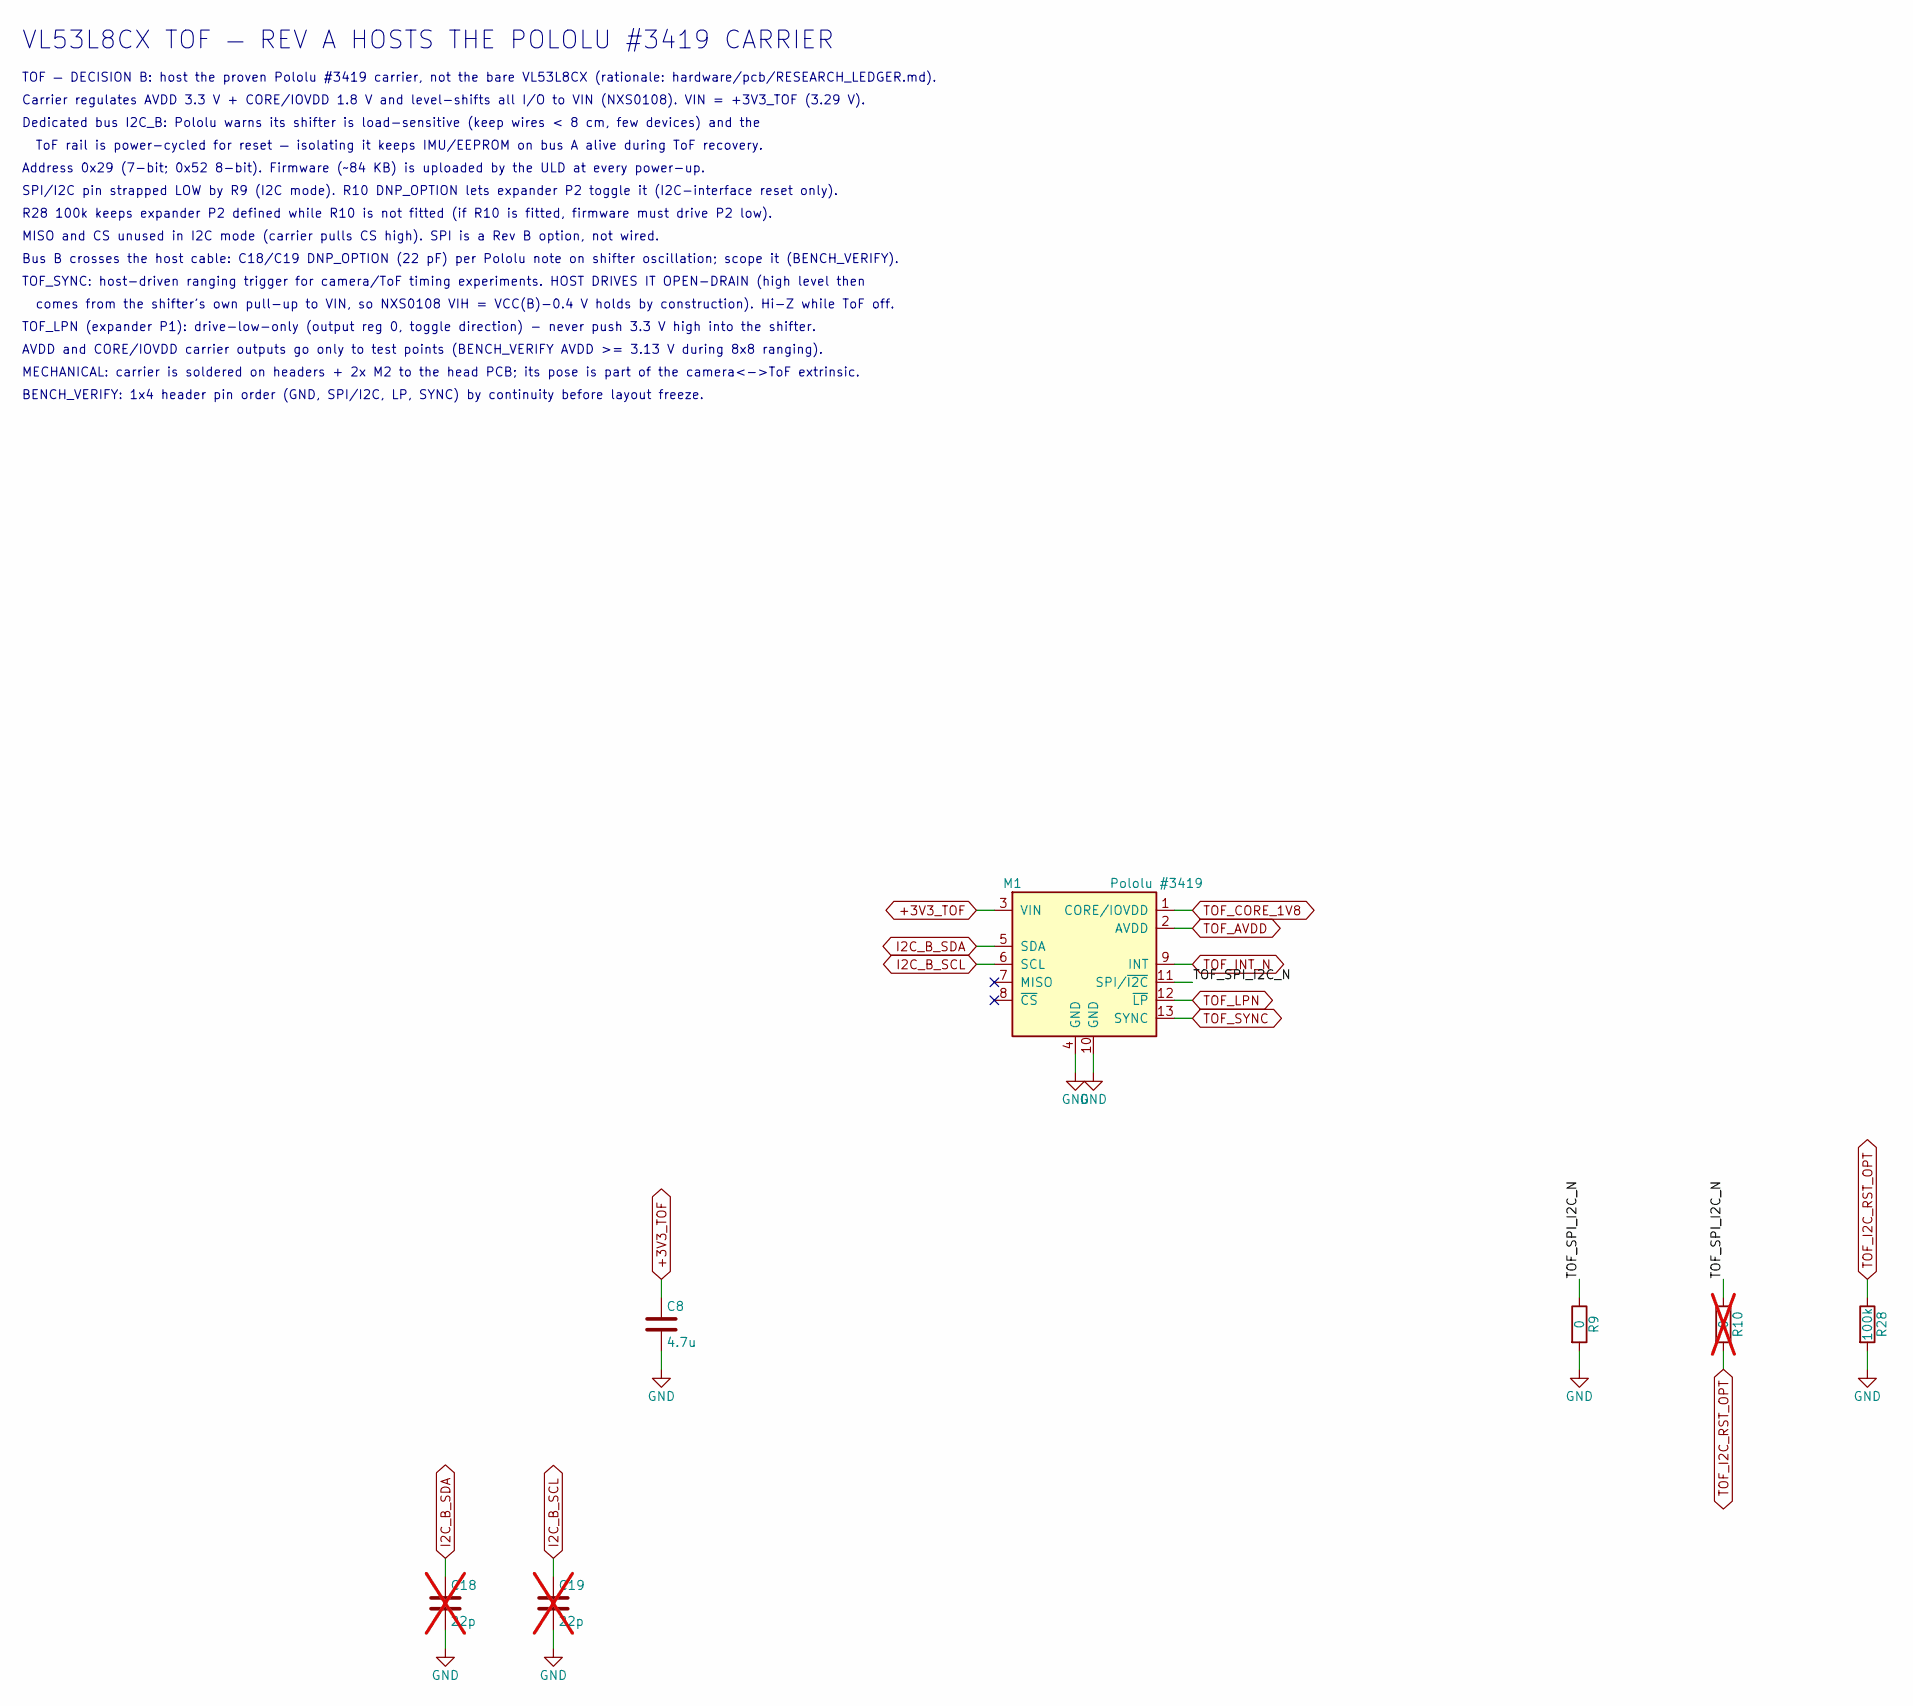
[picture p29: schematic tof.kicad_sch]

Parts:
C8: 4.7u; C_0805_2012Metric
C18, C19: 22p; C_0603_1608Metric; not fitted
M1: Pololu #3419; Pololu_3419_VL53L8CX_Carrier_THT; MPN 3419
R9: 0; R_0603_1608Metric
R10: 0; R_0603_1608Metric; not fitted
R28: 100k; R_0603_1608Metric

Connections:
+3V3_TOF: C8.1, M1.3 (VIN)
GND: C8.2, C18.2, C19.2, M1.4 (GND), M1.10 (GND), R9.2, R28.2
I2C_B_SCL: C19.1, M1.6 (SCL)
I2C_B_SDA: C18.1, M1.5 (SDA)
TOF_AVDD: M1.2 (AVDD)
TOF_CORE_1V8: M1.1 (CORE/IOVDD)
TOF_I2C_RST_OPT: R10.2, R28.1
TOF_INT_N: M1.9 (INT)
TOF_LPN: M1.12 (~LP)
TOF_SPI_I2C_N: M1.11 (SPI/~I2C), R9.1, R10.1
TOF_SYNC: M1.13 (SYNC)

Notes on the sheet:
VL53L8CX TOF — REV A HOSTS THE POLOLU #3419 CARRIER
TOF — DECISION B: host the proven Pololu #3419 carrier, not the bare VL53L8CX (rationale: hardware/pcb/RESEARCH_LEDGER.md).
Carrier regulates AVDD 3.3 V + CORE/IOVDD 1.8 V and level-shifts all I/O to VIN (NXS0108). VIN = +3V3_TOF (3.29 V).
Dedicated bus I2C_B: Pololu warns its shifter is load-sensitive (keep wires < 8 cm, few devices) and the
ToF rail is power-cycled for reset — isolating it keeps IMU/EEPROM on bus A alive during ToF recovery.
Address 0x29 (7-bit; 0x52 8-bit). Firmware (~84 KB) is uploaded by the ULD at every power-up.
SPI/I2C pin strapped LOW by R9 (I2C mode). R10 DNP_OPTION lets expander P2 toggle it (I2C-interface reset only).
R28 100k keeps expander P2 defined while R10 is not fitted (if R10 is fitted, firmware must drive P2 low).
MISO and CS unused in I2C mode (carrier pulls CS high). SPI is a Rev B option, not wired.
Bus B crosses the host cable: C18/C19 DNP_OPTION (22 pF) per Pololu note on shifter oscillation; scope it (BENCH_VERIFY).
TOF_SYNC: host-driven ranging trigger for camera/ToF timing experiments. HOST DRIVES IT OPEN-DRAIN (high level then
comes from the shifter's own pull-up to VIN, so NXS0108 VIH = VCC(B)-0.4 V holds by construction). Hi-Z while ToF off.
TOF_LPN (expander P1): drive-low-only (output reg 0, toggle direction) - never push 3.3 V high into the shifter.
AVDD and CORE/IOVDD carrier outputs go only to test points (BENCH_VERIFY AVDD >= 3.13 V during 8x8 ranging).
MECHANICAL: carrier is soldered on headers + 2x M2 to the head PCB; its pose is part of the camera<->ToF extrinsic.
BENCH_VERIFY: 1x4 header pin order (GND, SPI/I2C, LP, SYNC) by continuity before layout freeze.
